colestriler/codex-micro-diy-guide/pcb/led-driver-rev-a/board-top.png

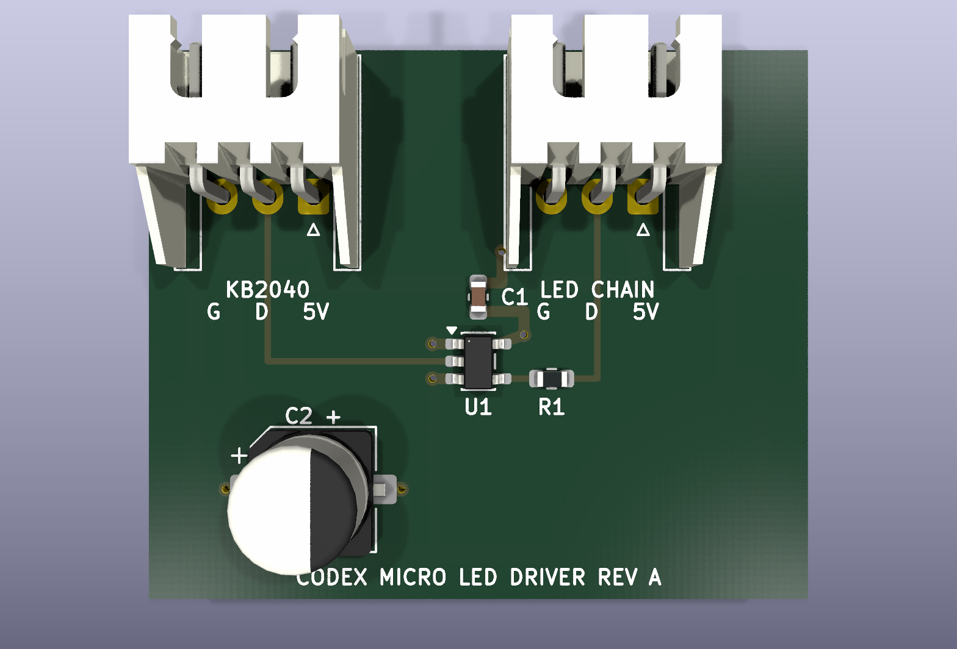
pcb/led-driver-rev-a/board-top.png
