colestriler/codex-micro-diy-guide/public/downloads/joystick-flat-v3/preview.png

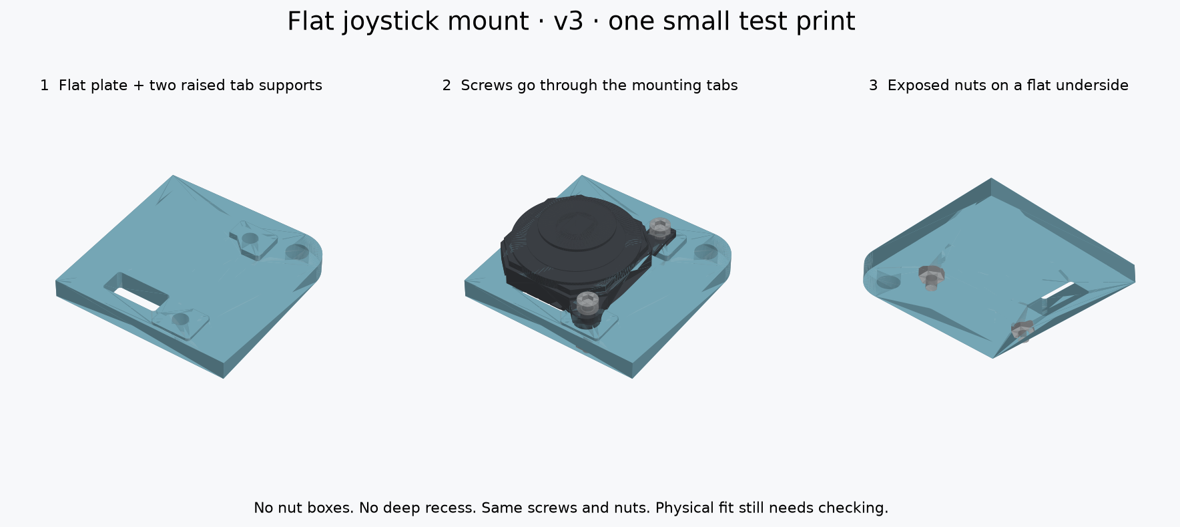
public/downloads/joystick-flat-v3/preview.png
