colestriler/codex-micro-diy-guide/public/downloads/mounting-v5/preview.png

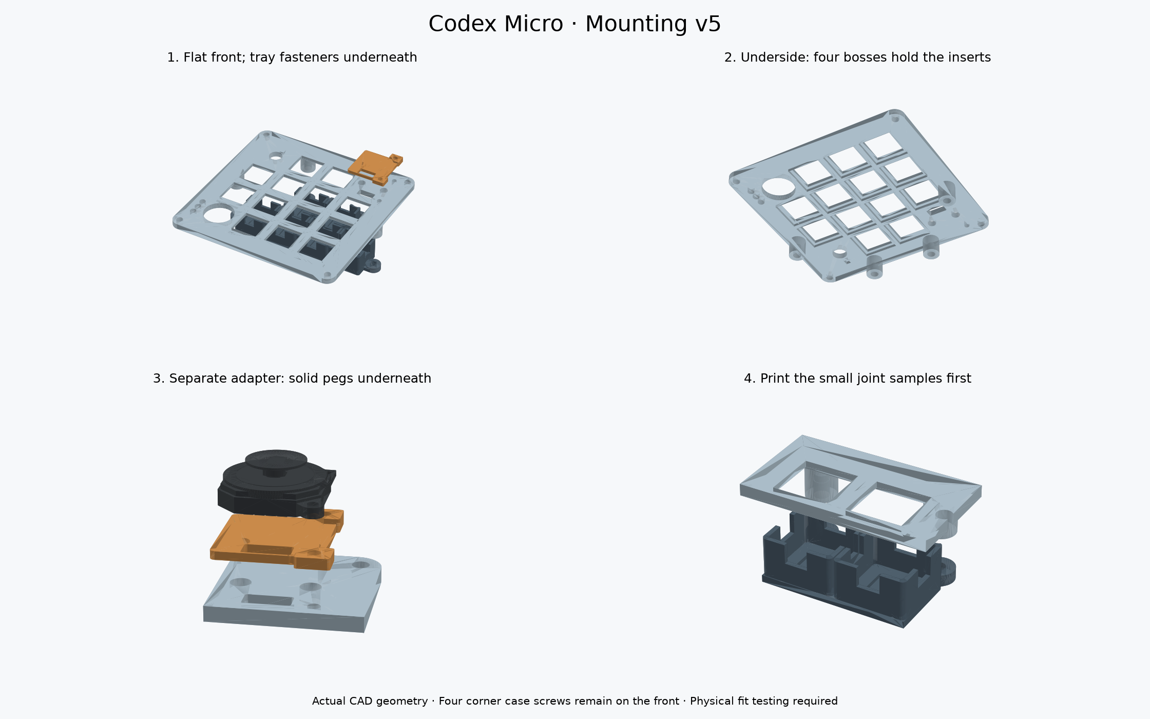
public/downloads/mounting-v5/preview.png
