colestriler/codex-micro-diy-guide/public/downloads/mounting-v5/files/PRINT_FIRST_lower_joint_sample.step

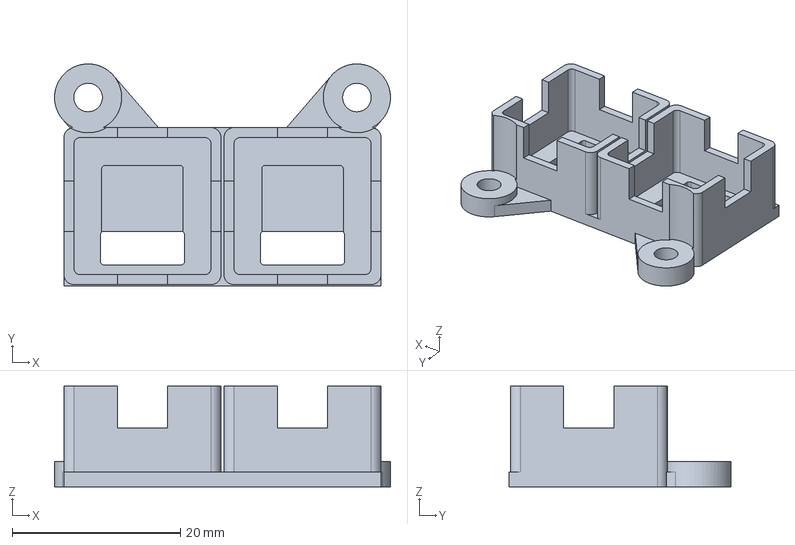
[picture p22: CAD file, 2026-09-16]
public/downloads/mounting-v5/files/PRINT_FIRST_lower_joint_sample.step
40.0 x 26.4 x 12.0 mm
