colestriler/codex-micro-diy-guide/public/downloads/mounting-v5/references/tray-v4.step

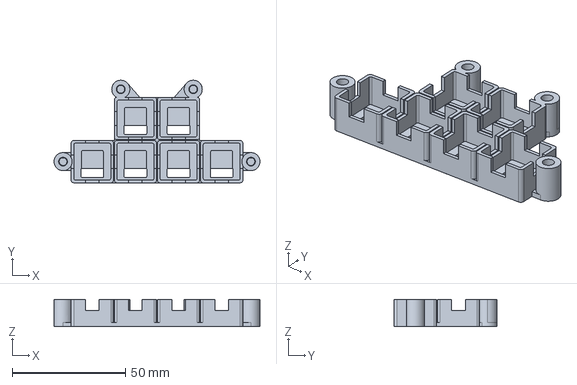
[picture p23: CAD file, 2026-09-15]
public/downloads/mounting-v5/references/tray-v4.step
91.0 x 45.3 x 12.0 mm
