colestriler/codex-micro-diy-guide/public/downloads/baffle-snap-v1/files/PRINT_ONE_test_plate_with_clips.step

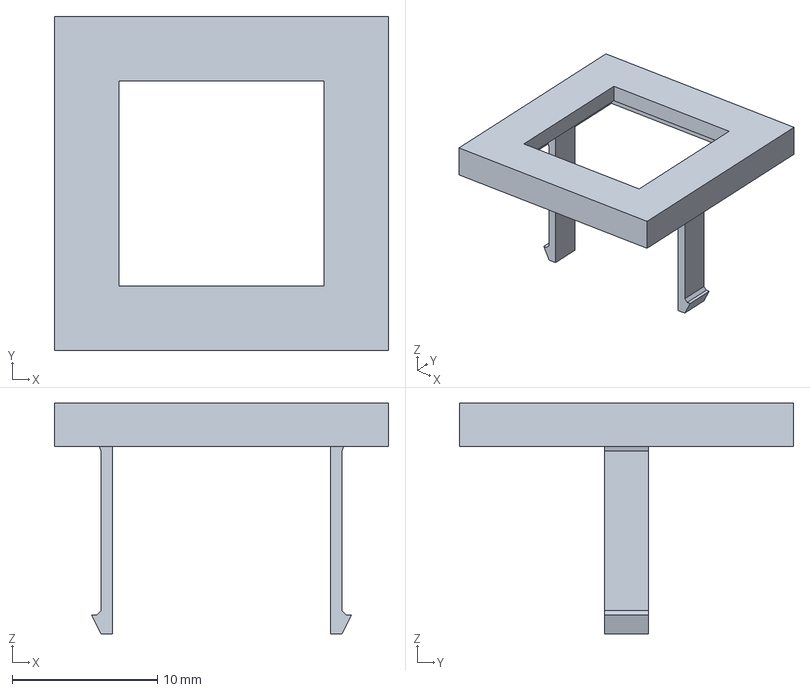
[picture p24: CAD file, 2026-09-15]
public/downloads/baffle-snap-v1/files/PRINT_ONE_test_plate_with_clips.step
23.0 x 23.0 x 15.9 mm
