colestriler/codex-micro-diy-guide/public/downloads/baffle-tray-v4/files/PRINT_FIRST_two_key_top_sample.step

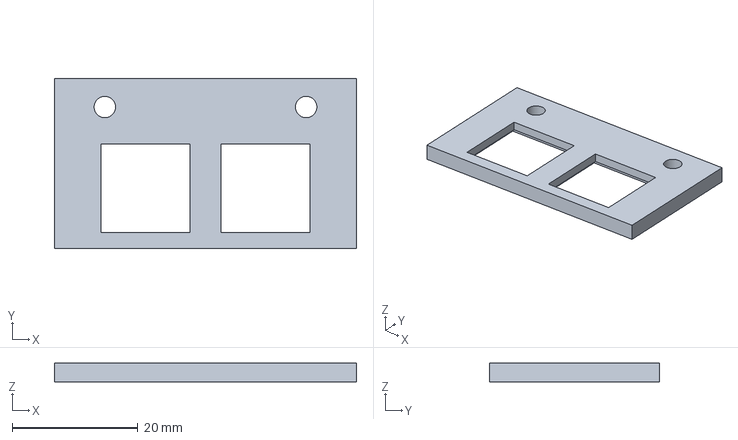
[picture p25: CAD file, 2026-09-15]
public/downloads/baffle-tray-v4/files/PRINT_FIRST_two_key_top_sample.step
48.0 x 26.9 x 3.00 mm
