colestriler/codex-micro-diy-guide/public/downloads/joystick-fit-v1/files/holder.step

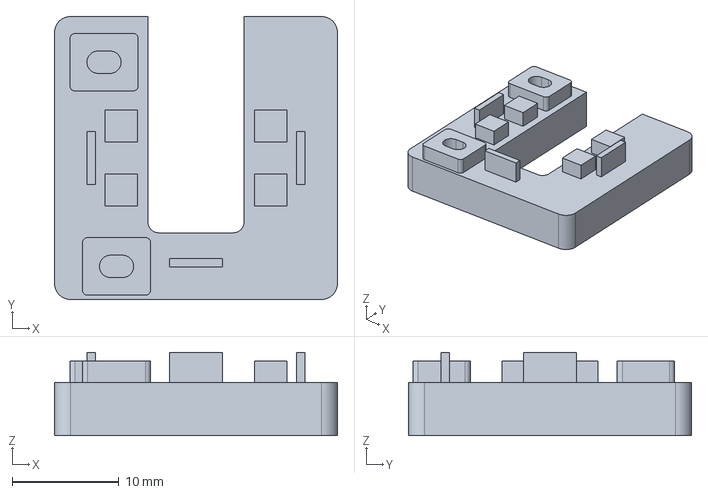
[picture p26: CAD file, 2026-09-14]
public/downloads/joystick-fit-v1/files/holder.step
26.5 x 26.5 x 7.80 mm
