colestriler/codex-micro-diy-guide/public/downloads/mounting-v5/files/PRINT_FIRST_joystick_corner.step

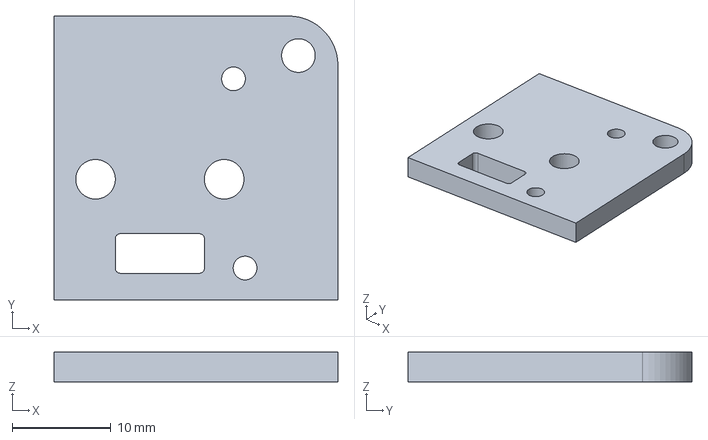
[picture p27: CAD file, 2026-09-16]
public/downloads/mounting-v5/files/PRINT_FIRST_joystick_corner.step
28.7 x 28.7 x 3.00 mm
