colestriler/codex-micro-diy-guide/public/downloads/mounting-v5/references/joystick-reference.step

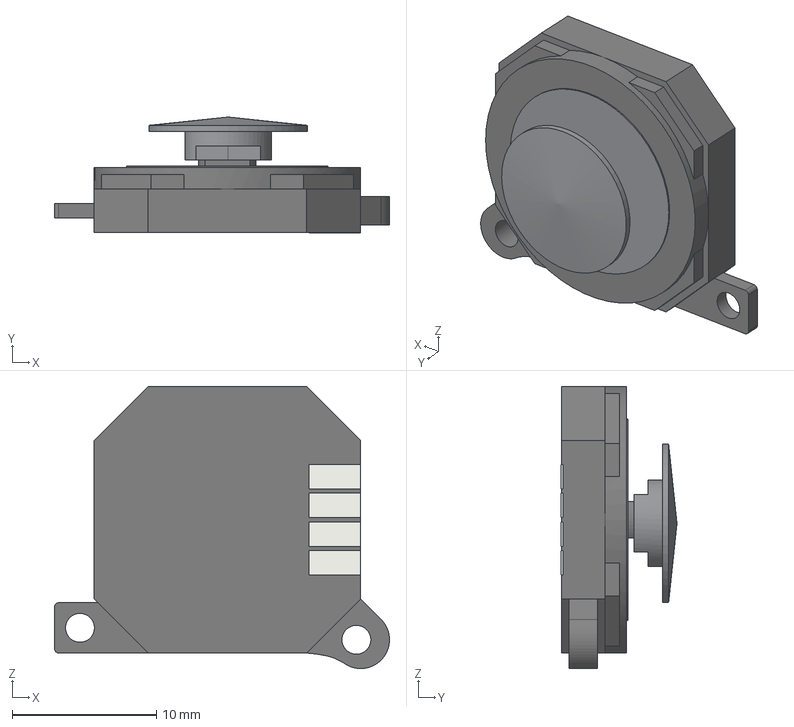
[picture p28: CAD file, 2026-09-14]
public/downloads/mounting-v5/references/joystick-reference.step
23.2 x 8.05 x 19.6 mm
