colestriler/codex-micro-diy-guide/public/downloads/step/07_light_tray_v5_WAIT.step

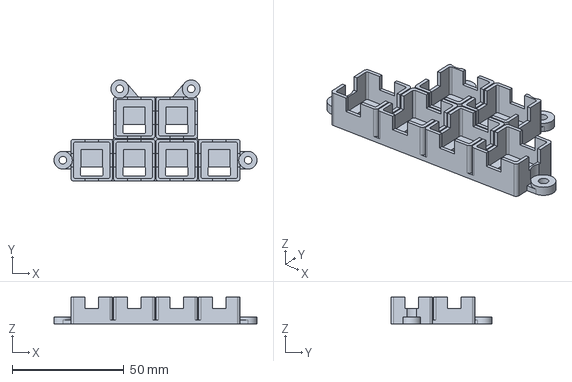
[picture p29: CAD file, 2026-09-16]
public/downloads/step/07_light_tray_v5_WAIT.step
91.0 x 45.3 x 12.0 mm
