colestriler/codex-micro-diy-guide/public/downloads/baffle-tray-v4/files/PRINT_FIRST_two_key_baffle_sample.step

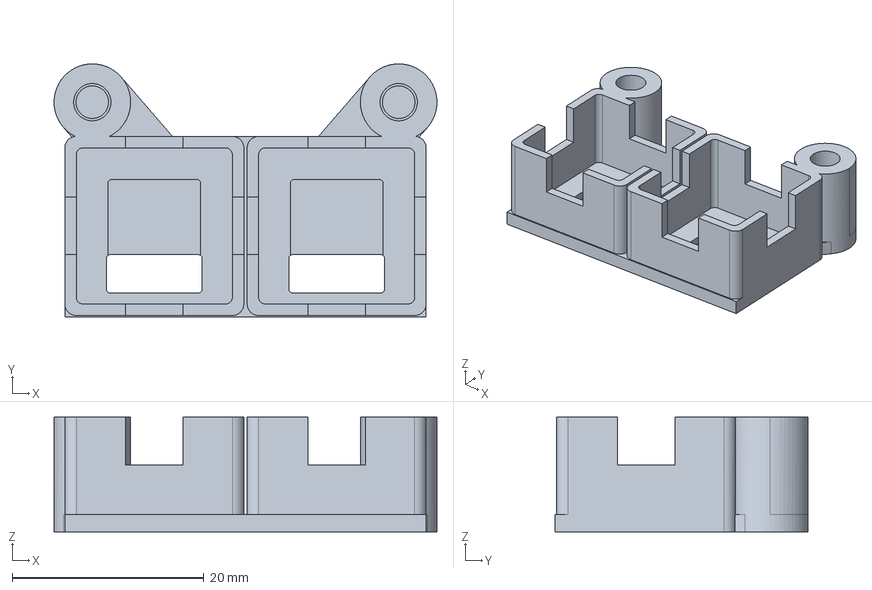
[picture p30: CAD file, 2026-09-15]
public/downloads/baffle-tray-v4/files/PRINT_FIRST_two_key_baffle_sample.step
40.0 x 26.4 x 12.0 mm
