colestriler/codex-micro-diy-guide/public/downloads/joystick-fit-v1/files/shim_B_0.5mm.step

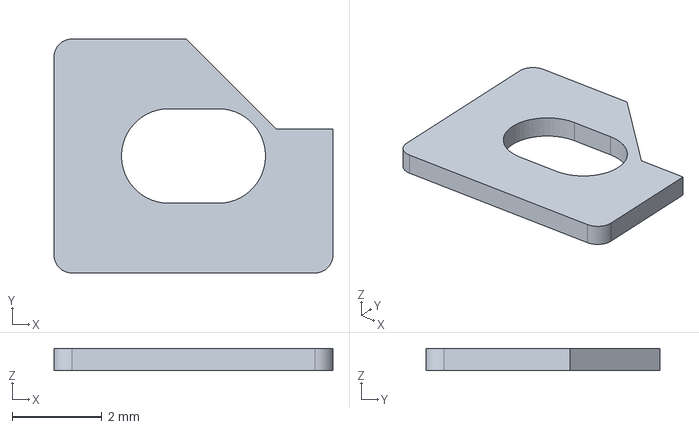
[picture p31: CAD file, 2026-09-14]
public/downloads/joystick-fit-v1/files/shim_B_0.5mm.step
6.20 x 5.20 x 0.5 mm
