colestriler/codex-micro-diy-guide/public/downloads/joystick-integrated-v2/files/PRINT_FIRST_joystick_corner_v2.step

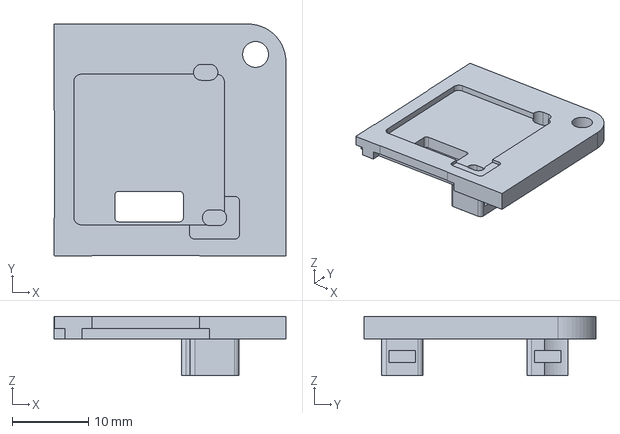
[picture p32: CAD file, 2026-09-14]
public/downloads/joystick-integrated-v2/files/PRINT_FIRST_joystick_corner_v2.step
30.5 x 30.5 x 7.80 mm
