colestriler/codex-micro-diy-guide/public/downloads/mounting-v5/references/case.step

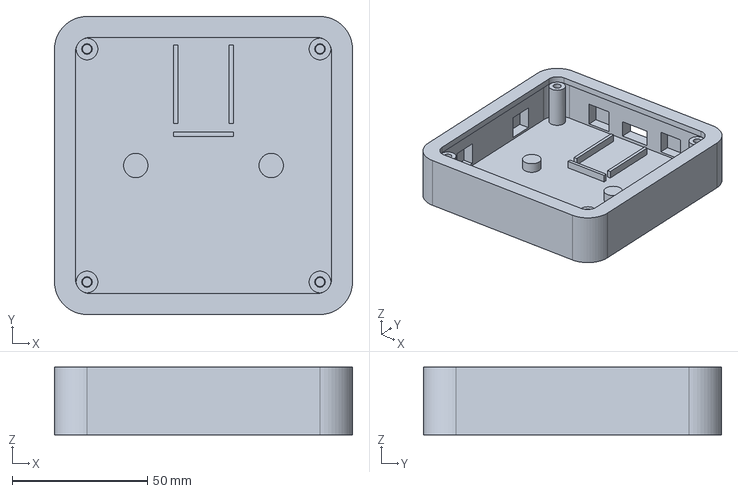
[picture p33: CAD file, 2026-09-06]
public/downloads/mounting-v5/references/case.step
110.0 x 110.0 x 25.0 mm
