colestriler/codex-micro-diy-guide/public/downloads/mounting-v5/references/original-plate.step

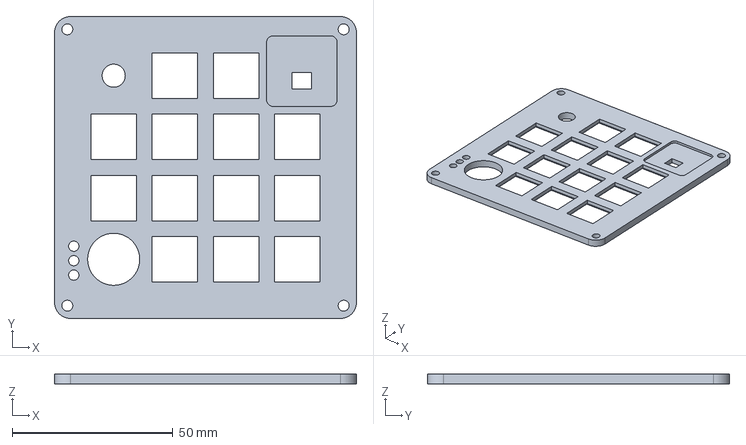
[picture p34: CAD file, 2026-09-06]
public/downloads/mounting-v5/references/original-plate.step
94.0 x 94.0 x 3.00 mm
