colestriler/codex-micro-diy-guide/public/downloads/mounting-v5/files/PRINT_FIRST_upper_joint_sample.step

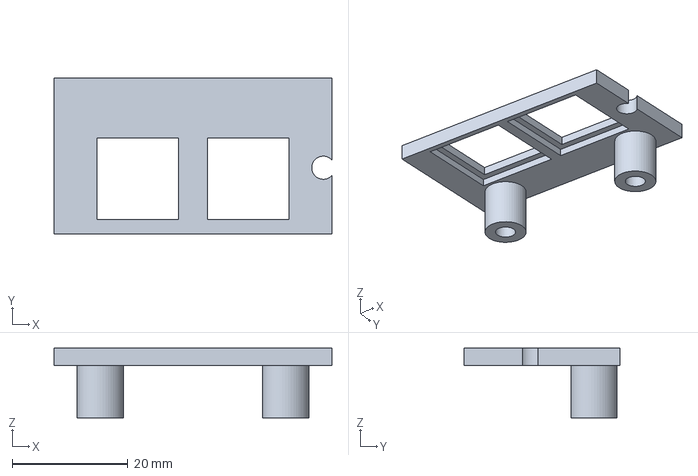
[picture p36: CAD file, 2026-09-16]
public/downloads/mounting-v5/files/PRINT_FIRST_upper_joint_sample.step
48.0 x 26.9 x 12.0 mm
