colestriler/codex-micro-diy-guide/public/downloads/step/04_joystick_adapter_v5.step

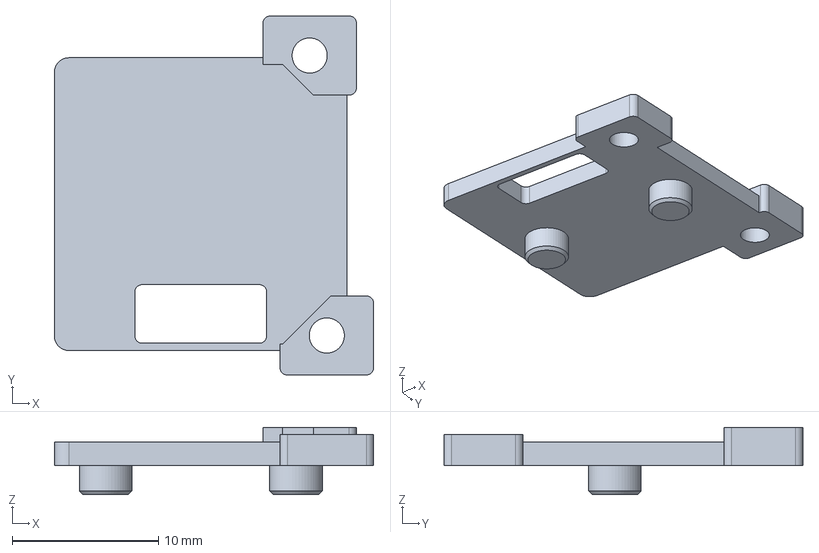
[picture p37: CAD file, 2026-09-16]
public/downloads/step/04_joystick_adapter_v5.step
21.8 x 24.5 x 4.60 mm
