colestriler/codex-micro-diy-guide/public/downloads/joystick-fit-v1/files/shim_B_1.0mm.step

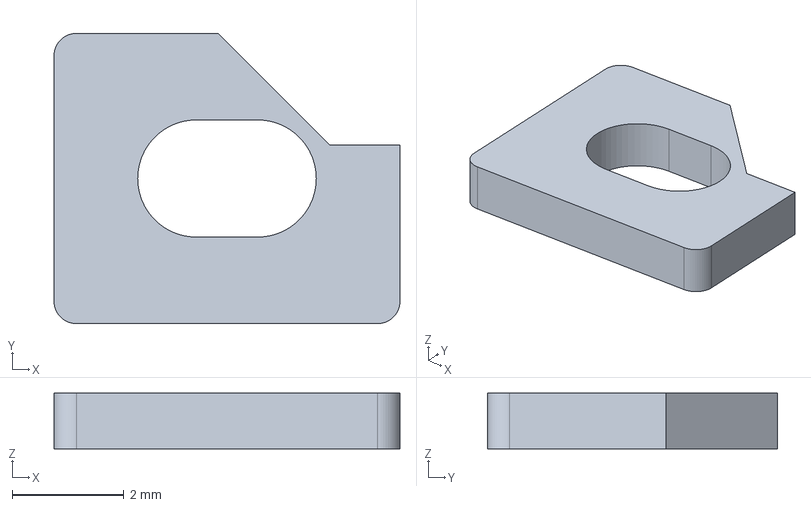
[picture p38: CAD file, 2026-09-14]
public/downloads/joystick-fit-v1/files/shim_B_1.0mm.step
6.20 x 5.20 x 1.00 mm
