colestriler/codex-micro-diy-guide/public/downloads/step/07_heatset_six_light_tray_v3_WAIT.step

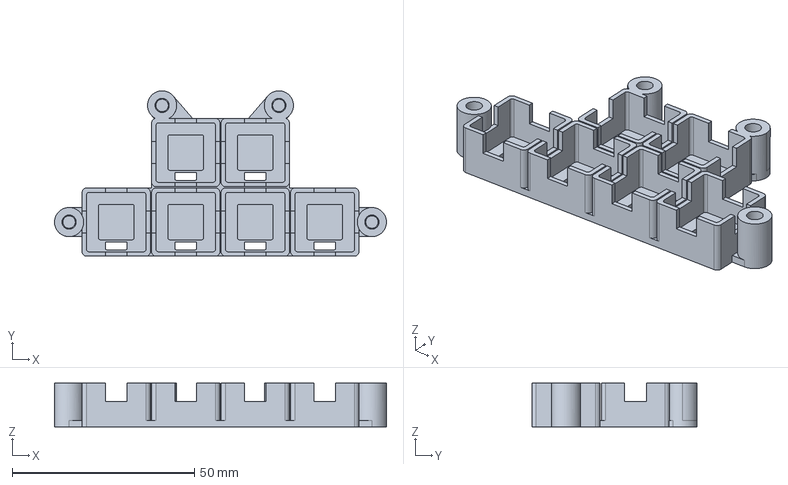
[picture p39: CAD file, 2026-09-15]
public/downloads/step/07_heatset_six_light_tray_v3_WAIT.step
91.0 x 45.3 x 12.0 mm
