colestriler/codex-micro-diy-guide/public/downloads/step/07_two_layer_baffle_sample.step

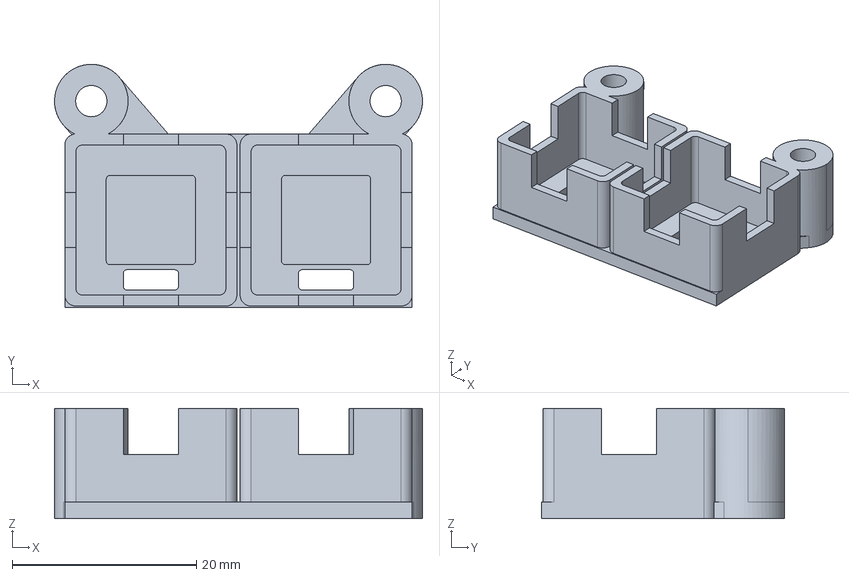
[picture p40: CAD file, 2026-09-15]
public/downloads/step/07_two_layer_baffle_sample.step
40.0 x 26.4 x 12.0 mm
