colestriler/codex-micro-diy-guide/public/downloads/step/09_keycap_2u_dual_stem.step

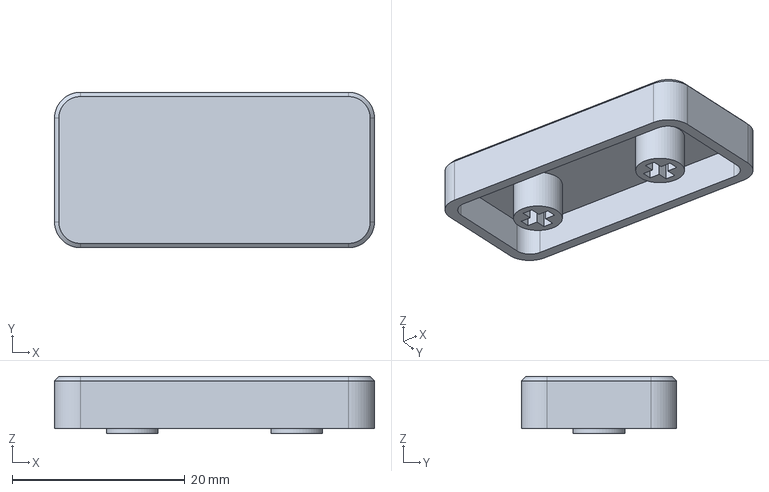
[picture p41: CAD file, 2026-09-13]
public/downloads/step/09_keycap_2u_dual_stem.step
37.0 x 18.0 x 6.60 mm
