colestriler/codex-micro-diy-guide/public/downloads/step/08_keycap_1u.step

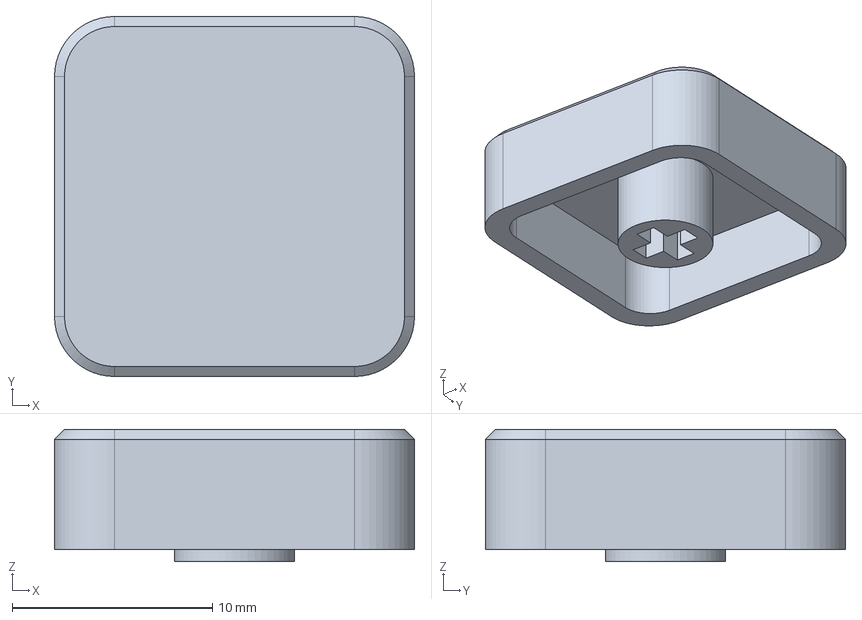
[picture p42: CAD file, 2026-09-13]
public/downloads/step/08_keycap_1u.step
18.0 x 18.0 x 6.60 mm
