colestriler/codex-micro-diy-guide/public/downloads/step/05_touch_cap.step

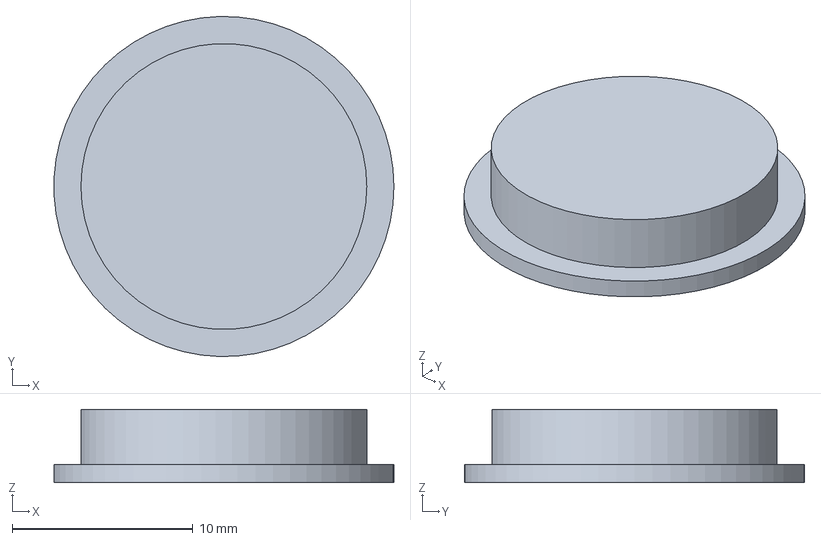
[picture p43: CAD file, 2026-09-06]
public/downloads/step/05_touch_cap.step
18.8 x 18.8 x 4.05 mm
