colestriler/codex-micro-diy-guide/public/downloads/step/04_joystick_cradle.step

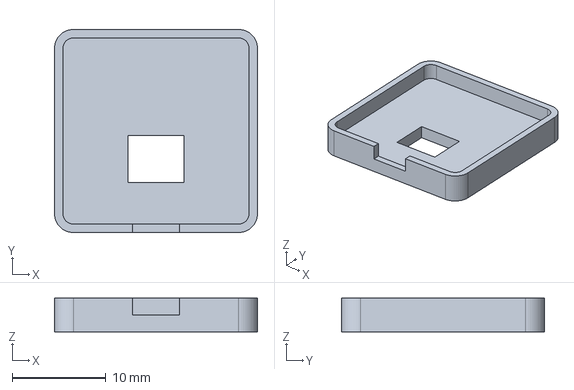
[picture p44: CAD file, 2026-09-06]
public/downloads/step/04_joystick_cradle.step
21.6 x 21.6 x 3.60 mm
