colestriler/codex-micro-diy-guide/public/downloads/step/11_stem_insert_coupon.step

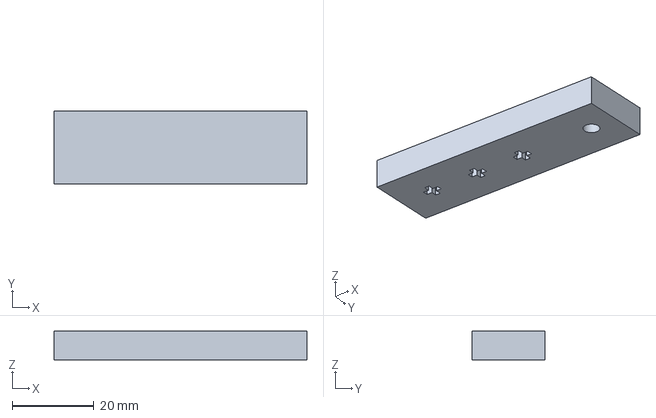
[picture p45: CAD file, 2026-09-06]
public/downloads/step/11_stem_insert_coupon.step
62.0 x 18.0 x 7.00 mm
