colestriler/codex-micro-diy-guide/public/downloads/step/03_round_foot.step

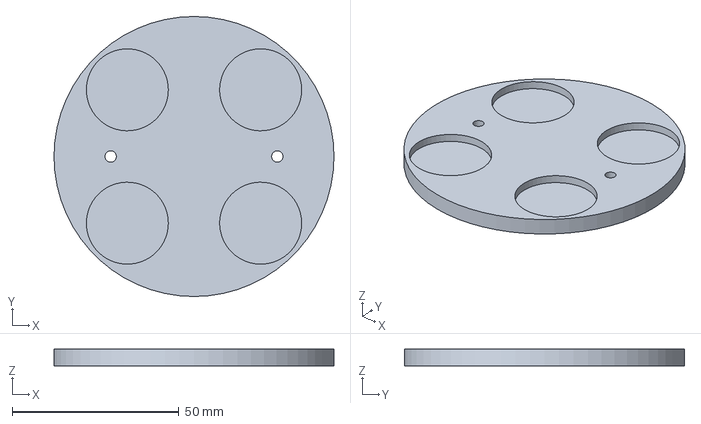
[picture p46: CAD file, 2026-09-06]
public/downloads/step/03_round_foot.step
84.0 x 84.0 x 5.00 mm
