colestriler/codex-micro-diy-guide/public/downloads/step/06_encoder_knob.step

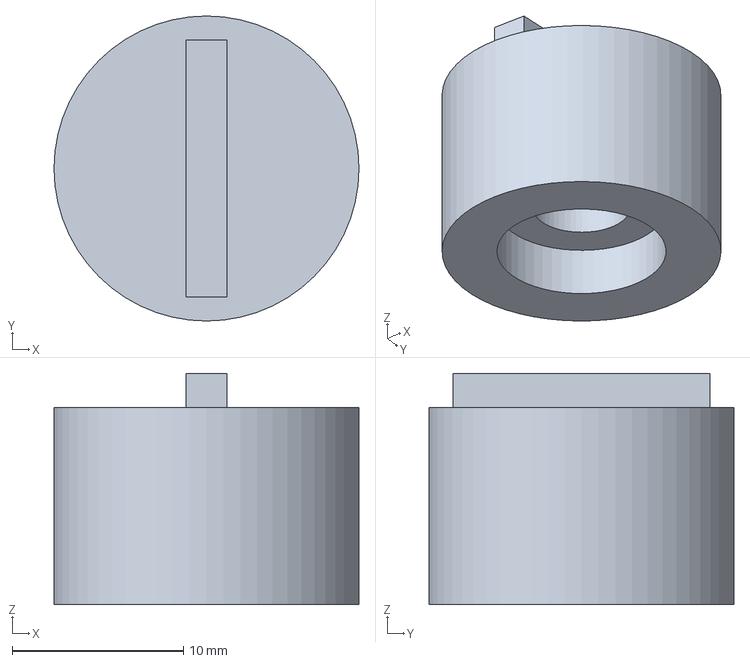
[picture p47: CAD file, 2026-09-06]
public/downloads/step/06_encoder_knob.step
17.8 x 17.8 x 13.5 mm
