colestriler/codex-micro-diy-guide/public/downloads/step/10_switch_fit_coupon.step

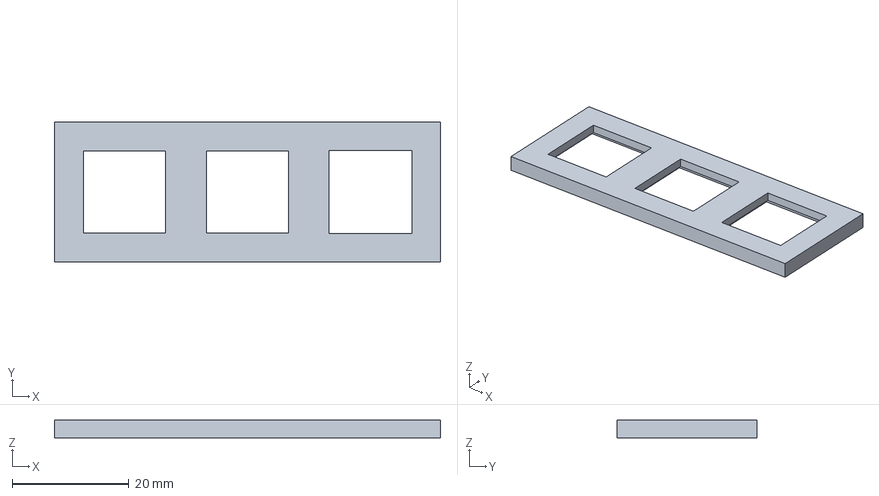
[picture p48: CAD file, 2026-09-06]
public/downloads/step/10_switch_fit_coupon.step
66.0 x 24.0 x 3.00 mm
