colestriler/codex-micro-diy-guide/public/downloads/wiring-guide/board-all.png

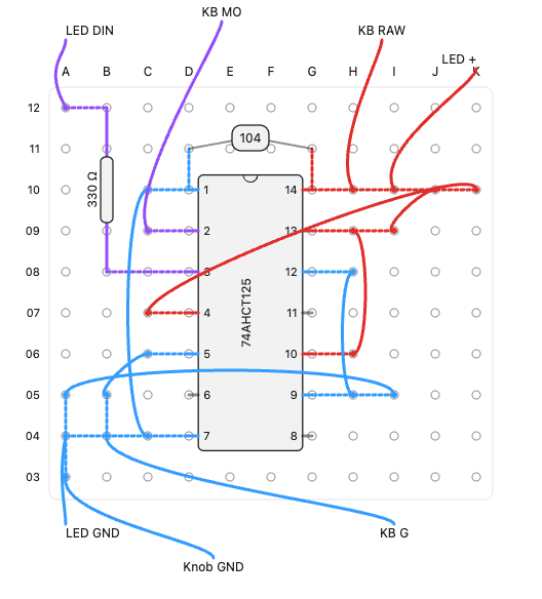
public/downloads/wiring-guide/board-all.png
