colestriler/codex-micro-diy-guide/public/downloads/wiring-guide/board-ground.png

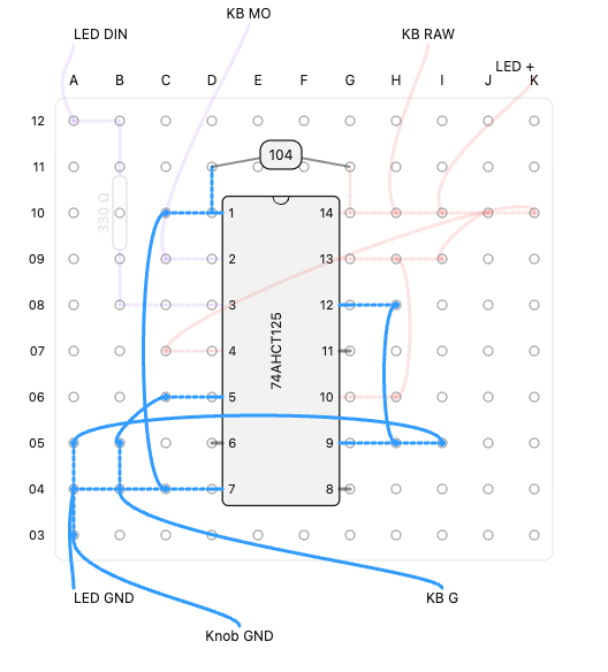
public/downloads/wiring-guide/board-ground.png
