colestriler/codex-micro-diy-guide/public/downloads/wiring-guide/board-power.png

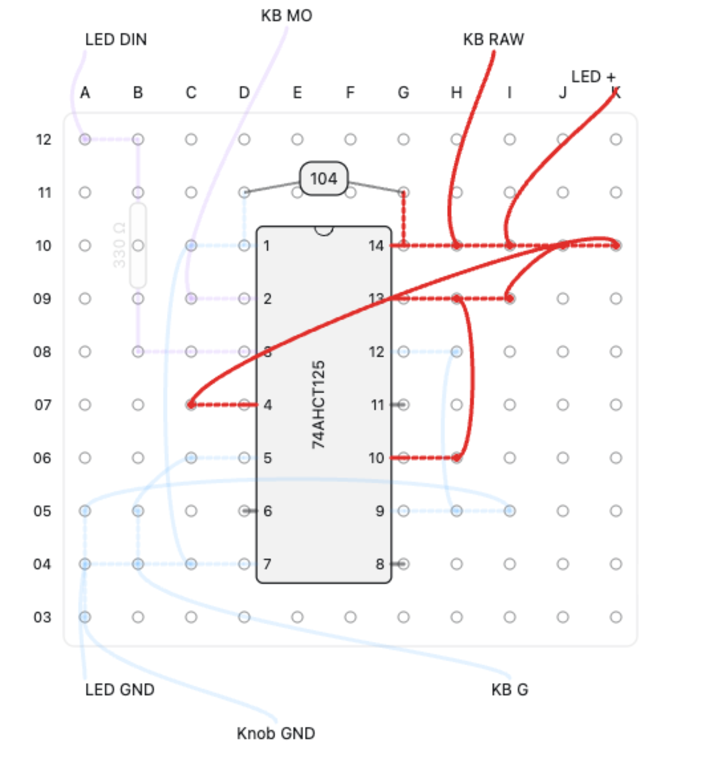
public/downloads/wiring-guide/board-power.png
