colestriler/codex-micro-diy-guide/public/downloads/wiring-guide/board-signal.png

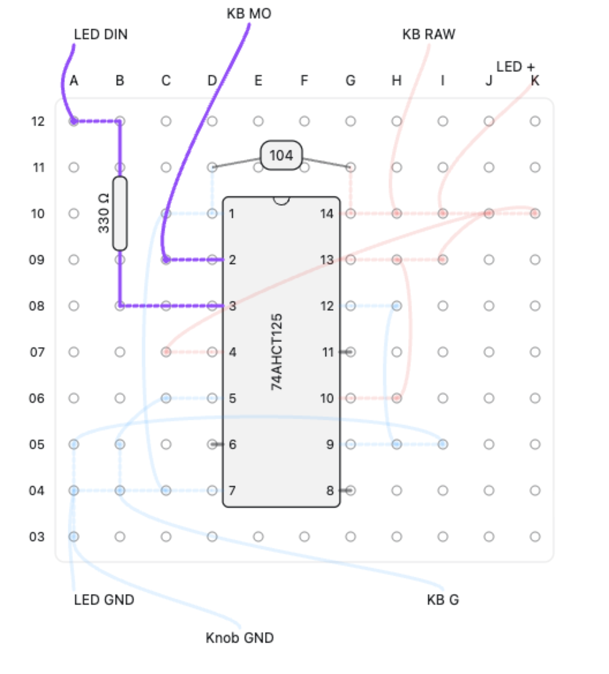
public/downloads/wiring-guide/board-signal.png
