colestriler/codex-micro-diy-guide/public/downloads/wiring-guide/complete-keyboard-preview.png

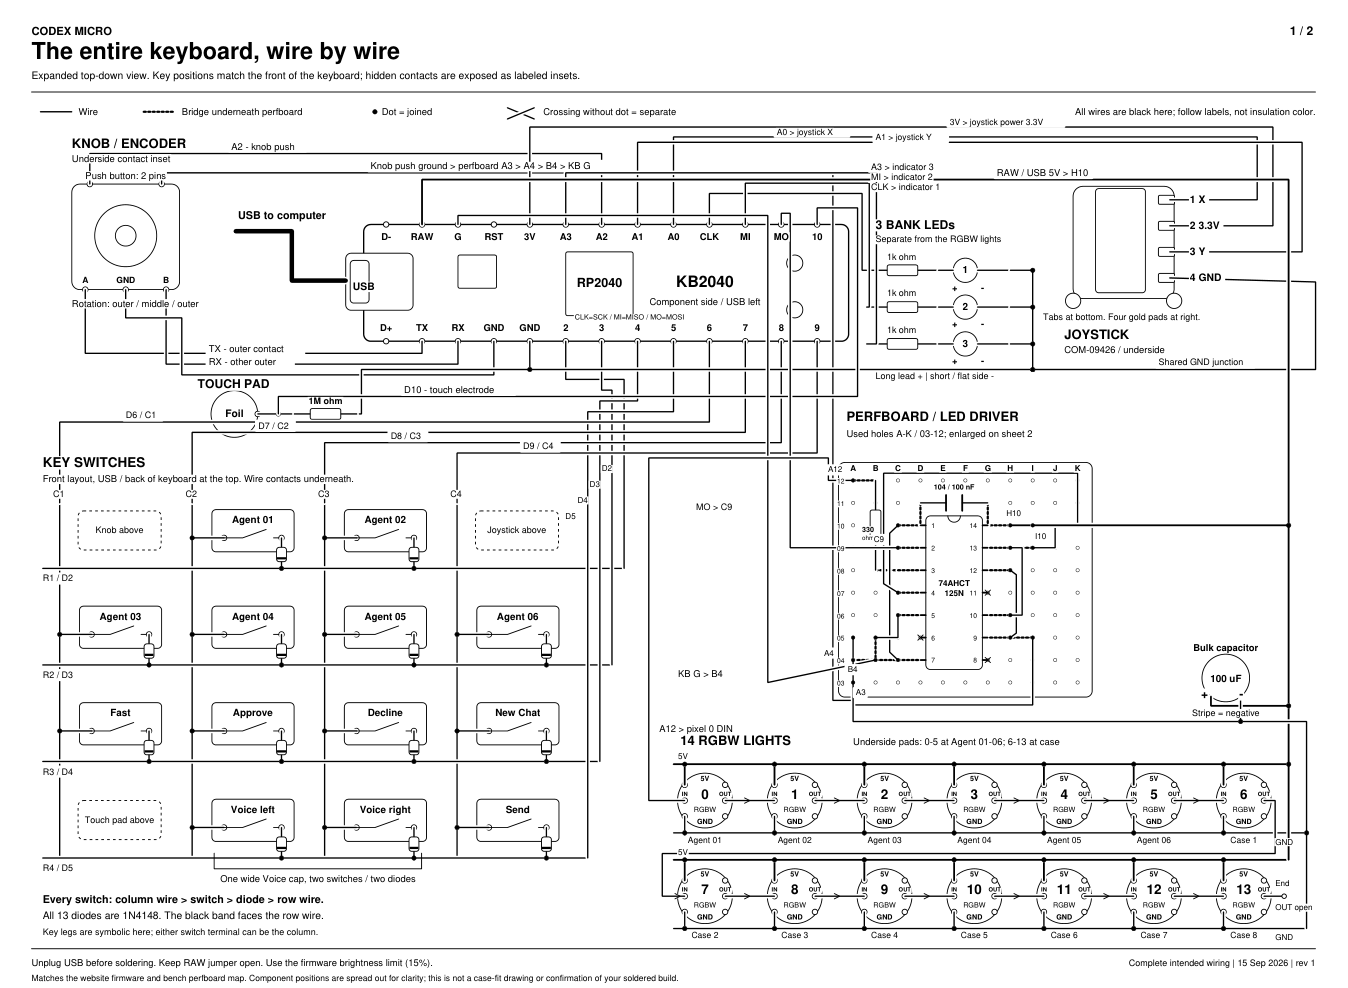
public/downloads/wiring-guide/complete-keyboard-preview.png
