colestriler/codex-micro-diy-guide/public/images/wiring/encoder.jpg

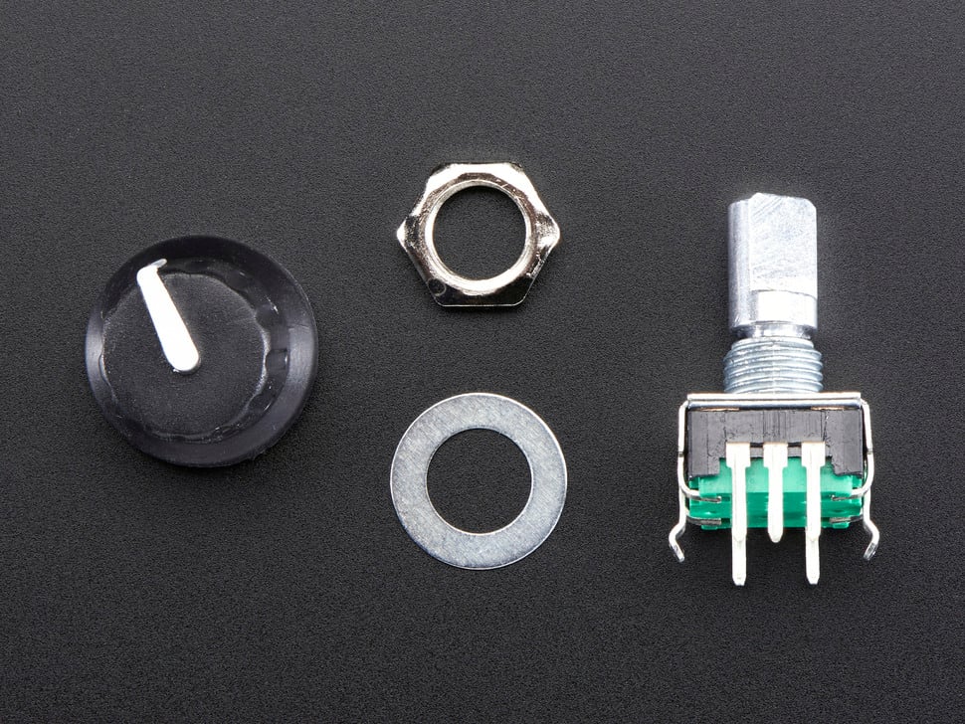
public/images/wiring/encoder.jpg
