colestriler/codex-micro-diy-guide/public/images/wiring/pixels.jpg

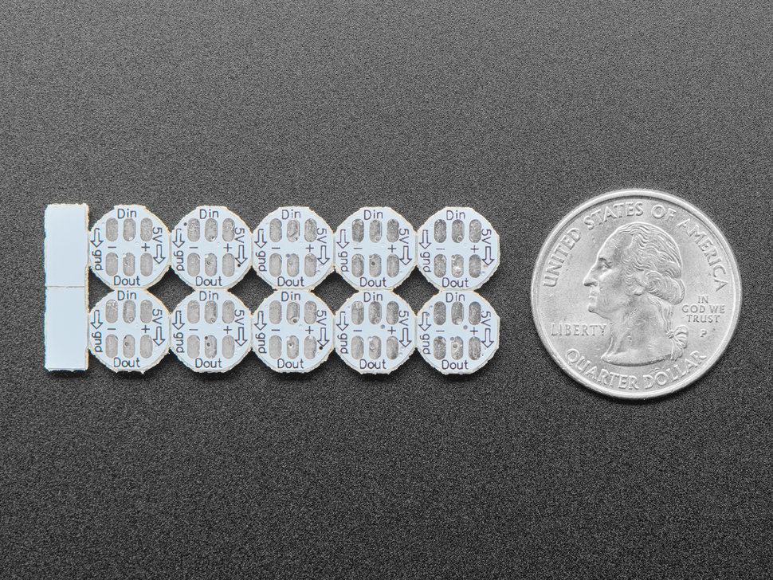
public/images/wiring/pixels.jpg
