colestriler/codex-micro-diy-guide/public/downloads/tools/make_guide.py

from pathlib import Path
import csv,json,base64,html,zipfile,io
ROOT=Path(__file__).resolve().parents[1]
PARTS=json.loads((ROOT/'docs/parts.json').read_text())

def dl(path,label=None):
    p=ROOT/path
    if not p.exists():raise FileNotFoundError(p)
    mime='application/octet-stream'
    return '<a download="'+html.escape(p.name)+'" href="data:'+mime+';base64,'+base64.b64encode(p.read_bytes()).decode()+'">'+html.escape(label or p.name)+'</a>'

def link(url,label):return '<a href="'+html.escape(url)+'" target="_blank" rel="noopener">'+label+' ↗</a>'
rows=''
materials={'01_case':'Clear / natural PETG','02_switch_plate':'White or clear PETG','03_round_foot':'White or gray PETG','04_joystick_cradle':'Black PETG','05_touch_cap':'Black PETG','06_encoder_knob':'White PETG','07_led_baffle':'Black PETG','08_keycap_1u':'6 clear + 5 white PETG','09_keycap_2u_dual_stem':'White PETG','10_switch_fit_coupon':'Same as plate','11_stem_insert_coupon':'Same as cap / case'}
for name,p in PARTS.items():
    rows+=f'<tr><td><strong>{html.escape(name.replace("_"," "))}</strong><small>{html.escape(p["notes"])}</small></td><td>{p["qty"]}</td><td>{materials[name]}</td><td>{dl("stl/"+name+".stl","STL")} · {dl("step/"+name+".step","STEP")}</td></tr>'
bom=''
for r in csv.DictReader((ROOT/'docs/bom.csv').open()):
    bom+=f'<tr data-route="{r["route"]}"><td><input type="checkbox" aria-label="Bought {html.escape(r["item"])}"></td><td><strong>{link(r["url"],html.escape(r["item"]))}</strong><small>{html.escape(r["notes"])}</small></td><td>{r["quantity_to_buy"]}<small>Use: {r["quantity_used"]}</small></td><td>{r["estimated_USD"]}</td><td><span class="tag">{r["route"]}</span></td></tr>'
# Embedded download makes the HTML usable as a single self-contained file.
packed=io.BytesIO()
with zipfile.ZipFile(packed,'w',zipfile.ZIP_DEFLATED) as z:
    for folder in ['cad','stl','step','firmware','tools','docs','animation']:
        for p in sorted((ROOT/folder).rglob('*')):
            if p.is_file() and '__pycache__' not in p.parts and p.name!='make_guide.py':z.write(p,p.relative_to(ROOT))
    for n in ['README.md','requirements.txt','assembly-animation.html']:z.write(ROOT/n,n)
zip_data=base64.b64encode(packed.getvalue()).decode()
preview=base64.b64encode((ROOT/'docs/cad-preview.png').read_bytes()).decode()
wiring=(ROOT/'docs/wiring.svg').read_text()
page='''<!doctype html>
<html lang="en"><head><meta charset="utf-8"><meta name="viewport" content="width=device-width, initial-scale=1"><title>DIY Micro — Full Build Specification</title>
<style>
:root{--ink:#152e2b;--muted:#5c7069;--paper:#f4f4ee;--line:#d6dfd7;--green:#b9d7ac;--dark:#163c33;--amber:#f4d496}*{box-sizing:border-box}html{scroll-behavior:smooth;scroll-padding-top:86px}body{margin:0;background:var(--paper);color:var(--ink);font:16px/1.65 -apple-system,BlinkMacSystemFont,"Segoe UI",sans-serif}a{color:#25614d;text-underline-offset:4px}a:hover{color:#102f23}button,input{font:inherit}button{cursor:pointer}header{position:sticky;top:0;background:rgba(244,244,238,.97);z-index:5;border-bottom:1px solid var(--line);padding:16px 4vw;display:flex;align-items:center;gap:26px}header .brand{font-weight:800;letter-spacing:-.6px;white-space:nowrap}nav{display:flex;gap:22px;overflow:auto;white-space:nowrap;font-size:13px;flex:1}nav a{text-decoration:none;color:var(--muted)}.print{border:1px solid var(--line);background:transparent;border-radius:6px;padding:6px 12px;font-size:12px}.wrap{max-width:1240px;margin:auto;padding:0 40px}section{padding:65px 0;border-bottom:1px solid var(--line)}.eyebrow{font:12px/1.4 ui-monospace,monospace;letter-spacing:1.6px;text-transform:uppercase;color:var(--muted)}h1{font-size:clamp(45px,6.2vw,86px);line-height:1.03;letter-spacing:-4.5px;font-weight:600;margin:23px 0}h2{font-size:36px;line-height:1.16;letter-spacing:-1.3px;font-weight:600;margin:14px 0 22px}h3{font-size:20px;letter-spacing:-.4px;margin:8px 0 12px}p{margin:12px 0}.lead{font-size:19px;line-height:1.6;color:var(--muted);max-width:620px}.hero{display:grid;grid-template-columns:1fr 1fr;gap:45px;align-items:center;padding:70px 0 42px}.hero-copy p{max-width:540px}.actions{display:flex;gap:12px;flex-wrap:wrap;margin:26px 0}.actions a,.primary{padding:11px 18px;border:1px solid var(--ink);border-radius:6px;text-decoration:none;font-size:14px;font-weight:600}.actions a:first-child,.primary{background:var(--dark);color:#fff}.meta{display:flex;gap:23px;font:12px ui-monospace,monospace;flex-wrap:wrap;color:var(--muted)}.notice{border-left:4px solid #b68a37;background:#ede7d6;padding:18px 22px;margin:24px 0}.notice strong{display:block;margin-bottom:4px}.note{background:#e6ece2;border:1px solid #cbd8c5;border-radius:8px;padding:20px 24px}.grid2{display:grid;grid-template-columns:1fr 1fr;gap:24px}.grid3{display:grid;grid-template-columns:repeat(3,1fr);gap:20px}.card{padding:25px;border:1px solid var(--line);border-radius:10px;background:#fafbf6}.tag{display:inline-block;font:11px ui-monospace,monospace;text-transform:uppercase;letter-spacing:.7px;background:#e5eade;color:#385245;padding:4px 7px;border-radius:4px}.tag.gold{background:#f2dfb8;color:#65511a}.card p{color:var(--muted)}.table-wrap{overflow:auto}table{border-collapse:collapse;width:100%;font-size:14px;text-align:left}th{font-size:11px;text-transform:uppercase;letter-spacing:1px;color:var(--muted);padding:12px 14px;background:#e6ece2}td{padding:16px 14px;border-bottom:1px solid var(--line);vertical-align:top}td small{display:block;font-size:12px;color:var(--muted);line-height:1.5;margin-top:5px}td:last-child{white-space:nowrap}small,.caption{font-size:12px;color:var(--muted)}code{background:#e5eae0;padding:2px 5px;border-radius:3px;font-size:13px}pre{background:#203b33;color:#ecf3e6;border-radius:8px;padding:22px;overflow:auto;font:13px/1.7 ui-monospace,monospace}pre code{background:none;padding:0;color:inherit}ul,ol{padding-left:22px}li{margin:9px 0}.steps{counter-reset:step;display:grid;grid-template-columns:1fr 1fr;gap:18px}.step{border:1px solid var(--line);background:#fafbf6;padding:24px;border-radius:8px}.step:before{counter-increment:step;content:counter(step,decimal-leading-zero);font:12px ui-monospace,monospace;color:#7c8f77;display:block;margin-bottom:10px}.step p{color:var(--muted);font-size:14px}.wide{grid-column:1/-1}.preview{display:block;width:100%;border-radius:9px}.downloads{display:flex;gap:18px;flex-wrap:wrap;margin:15px 0;font-size:14px}.swatch{height:85px;border-radius:6px;margin:16px 0;border:1px solid #d5dbd1}.clear{background:repeating-linear-gradient(115deg,#dce4da70 0 1px,#f9fcf870 1px 5px),linear-gradient(130deg,#d0e3da,#f5f7f2)}.white{background:#f9faf5}.black{background:#262f2a}.filters{display:flex;gap:8px;margin:20px 0;flex-wrap:wrap}.filters button,.status-btn{border:1px solid var(--line);border-radius:30px;padding:7px 15px;background:transparent;font-size:12px}.filters button.active{background:var(--dark);color:white}.sim{background:#dbe5d7;border-radius:16px;padding:30px;position:relative}.device{width:min(100%,380px);margin:10px auto 25px;padding:32px;background:linear-gradient(135deg,#f9faf5,#bec9c1);border:2px solid #eaf1e8;box-shadow:8px 20px 32px #52665529,0 8px 0 #9daea1;border-radius:36px;position:relative}.device-grid{display:grid;grid-template-columns:repeat(4,1fr);gap:7px;padding:8px;background:#e4e9e2;border-radius:13px}.key{aspect-ratio:1;border:1px solid #f7faf3;border-radius:12px;background:linear-gradient(135deg,#f9fbf4,#e1e7dc);color:#18392d;box-shadow:0 4px 0 #b4c0b1;display:flex;align-items:center;justify-content:center;font-size:22px;padding:0}.key svg{width:24px;height:24px;fill:none;stroke:currentColor;stroke-width:1.7;stroke-linecap:round;stroke-linejoin:round}.key.agent{background:radial-gradient(circle,var(--glow,#398cf0) 0,#ffffff36 72%),#c0d0ca;box-shadow:0 4px 0 #9dafaa,inset 0 0 20px var(--glow,#398cf0);font:11px ui-monospace,monospace;color:#19392e}.key.agent.selected{outline:2px solid #214d3c;outline-offset:2px}.key.knob{border-radius:50%;transform:rotate(35deg);font-size:36px}.key.joy{border-radius:50%;background:#26342c;border:5px solid #4e5f52;color:#a3b8a8;box-shadow:0 3px 0 #16291d;font-size:15px}.key.touch{border:none;background:radial-gradient(circle,#173328 0 30%,#a2b49f 33% 39%,transparent 41%);box-shadow:none}.key.wide-key{grid-column:span 2;aspect-ratio:auto}.sim .caption{text-align:center;margin-top:15px}.status-buttons{display:flex;gap:7px;flex-wrap:wrap;justify-content:center}.status-btn{background:#f4f7ef;display:flex;align-items:center;gap:6px}.dot{display:inline-block;width:8px;height:8px;border-radius:50%;background:var(--c);box-shadow:0 0 0 1px #172c2120}.sim-status{text-align:center;font-size:13px;margin:14px 0 0}.status-line{display:flex;gap:10px;align-items:center;margin:8px 0}.status-line .dot{width:13px;height:13px}.progress{font:12px ui-monospace,monospace;color:var(--muted);margin:15px 0}input[type=checkbox]{accent-color:#39795b;width:16px;height:16px}.checklist label{display:block;padding:9px 0;font-size:14px}.checklist input{vertical-align:middle;margin-right:9px}.diagram svg{width:100%;height:auto}.footer{padding:35px 0 60px;font-size:12px;color:var(--muted)}.assembly-frame{width:100%;height:950px;border:1px solid var(--line);border-radius:10px;background:var(--paper)}@media(max-width:1050px){.assembly-frame{height:1150px}}@media(max-width:600px){.assembly-frame{height:1250px}}@media print{.assembly-frame{display:none}}.callout-number{font-size:35px;letter-spacing:-1px}.muted{color:var(--muted)}.hidden{display:none}@media(max-width:850px){.wrap{padding:0 22px}.hero,.grid2,.grid3,.steps{grid-template-columns:1fr}.hero{padding-top:35px}h1{letter-spacing:-2.5px}header{padding:14px 20px;gap:18px}header .print{display:none}section{padding:45px 0}.sim{max-width:500px;width:100%;margin:auto}td{min-width:100px}td:first-child{min-width:35px}.wide{grid-column:auto}}@media print{header,.actions,.filters,.status-buttons,.downloads,.print{display:none}body{font-size:11px;background:white}.wrap{padding:0}.hero{padding:0;gap:20px}h1{font-size:40px}h2{font-size:25px}section{padding:20px 0}a{color:inherit}td{padding:8px}.card,.step{break-inside:avoid}.sim{padding:15px}.device{max-width:250px;padding:20px}.key{font-size:15px}.notice{background:#eee}.hidden{display:table-row}}
</style></head><body>
<header><div class="brand">DIY / MICRO</div><nav aria-label="Build guide"><a href="#route">Build route</a><a href="#plastic">Plastic</a><a href="#cad">CAD files</a><a href="#parts">Shopping list</a><a href="#animation">Animation</a><a href="#assembly">Assembly</a><a href="#software">Software</a><a href="#checks">Validation</a></nav><button class="print" onclick="window.print()">Print guide</button></header>
<main class="wrap">
<div class="hero"><div class="hero-copy"><div class="eyebrow">Build specification · revision A · 06 Sep 2026</div><h1>Codex Micro.<br>A DIY build.</h1><p class="lead">Recreate the Codex Micro’s layout, tactile controls, and illuminated keys—with editable CAD and a complete parts plan.</p><div class="actions"><a download="DIY-Micro-CAD-and-build-files.zip" href="data:application/zip;base64,__ZIP__">Download all build files ↓</a><a href="#animation">Watch assembly →</a><a href="#route">Read the full-function route</a></div><div class="meta"><span>110 × 110 mm prototype</span><span>13 switches</span><span>6 agent keys</span></div></div>
<div class="sim"><div class="eyebrow">Color behavior / interactive illustration</div><div class="device"><div class="device-grid">
<div class="key knob" title="Reasoning / navigation dial">┃</div><button class="key agent selected" data-agent="0" aria-label="Select agent key 1">01</button><button class="key agent" data-agent="1" aria-label="Select agent key 2">02</button><div class="key joy" title="Planar joystick">✣</div>
<button class="key agent" data-agent="2" aria-label="Select agent key 3">03</button><button class="key agent" data-agent="3" aria-label="Select agent key 4">04</button><button class="key agent" data-agent="4" aria-label="Select agent key 5">05</button><button class="key agent" data-agent="5" aria-label="Select agent key 6">06</button>
<div class="key" title="Fast mode">ϟ</div><div class="key" title="Approve">✓</div><div class="key" title="Decline">×</div><div class="key" title="Continue in new chat">↗</div>
<div class="key touch" title="Touch input"></div><div class="key wide-key" title="Push to talk"><svg viewBox="0 0 24 24"><rect x="9" y="3" width="6" height="12" rx="3"/><path d="M6 11v1a6 6 0 0 0 12 0v-1M12 18v3M9 21h6"/></svg></div><div class="key" title="Send message">↵</div></div></div>
<div class="status-buttons"><button class="status-btn" data-state="idle"><i class="dot" style="--c:#f9faf5"></i>Idle</button><button class="status-btn" data-state="thinking"><i class="dot" style="--c:#4a92ff"></i>Thinking</button><button class="status-btn" data-state="complete"><i class="dot" style="--c:#63ce82"></i>Complete</button><button class="status-btn" data-state="input"><i class="dot" style="--c:#ffbd58"></i>Needs input</button><button class="status-btn" data-state="error"><i class="dot" style="--c:#f3656a"></i>Error</button><button class="status-btn" data-state="off"><i class="dot" style="--c:#8c9b90"></i>Off</button></div><div class="sim-status" aria-live="polite">Agent 01 · Thinking</div><p class="caption">Select a key, then a state. This illustrates color meaning;<br>it is not connected to Codex and is not a color calibration.</p></div></div>
<div class="notice"><strong>Exact functionality is an electronics + software requirement.</strong>The included CAD and KB2040 firmware are a custom prototype. They do <b>not</b> currently deliver native Codex integration. For documented native behavior, use a genuine <b>Creator Micro 2</b> or <b>Codex Micro</b> with its original firmware. Re-housing that board requires measured donor geometry; the current printable case is <b>not a verified donor fit</b>.</div>
<section id="route"><div class="eyebrow">01 / choose the build that meets your requirement</div><h2>Keep the native electronics<br>for native Codex behavior.</h2><p>OpenAI explicitly lists Creator Micro 2 as compatible. The model with Bluetooth is the <b>Pro</b>; the Base is wired. A verified OEM PCB-only kit was not found. If matching the original is the priority, start with a complete genuine unit, verify it works, and customize its enclosure only after measuring it. <a href="https://learn.chatgpt.com/docs/features/codex-micro" target="_blank" rel="noopener">OpenAI compatibility guide ↗</a> · <a href="https://worklouder.cc/creator-micro-2" target="_blank" rel="noopener">Manufacturer specifications ↗</a></p>
<div class="grid2"><article class="card"><span class="tag">Recommended for your requirement</span><h3>Native electronics + printed exterior</h3><p>Retain the factory controller, LEDs, touch electrode, switch assembly, firmware, diffuser, and—on Pro—the original battery and charging circuit. That preserves the supported connection to Codex.</p><p><b>What still needs work:</b> measure the donor PCB, mounting holes, connectors, antenna and diffuser; then revise the case. No donor-compatible enclosure is claimed in this package.</p><p><a href="https://worklouder.cc/creator-micro-2" target="_blank" rel="noopener">Creator Micro 2 Pro ↗</a> · <a href="https://openai.com/supply/co-lab/work-louder/" target="_blank" rel="noopener">Codex Micro ↗</a></p><small>Availability: Codex Micro page showed out of stock ($230). Creator Micro 2 page showed “Not available” without a price. Confirm the selected variant at purchase; no order was placed.</small></article>
<article class="card"><span class="tag gold">Prototype / additional development</span><h3>Custom electronics + supplied CAD</h3><p>USB-C KB2040, hand-wired switches, planar joystick, rotary encoder, capacitive touch, six key LEDs and eight perimeter LEDs. The files below form a buildable prototype design, subject to physical fit and electrical testing.</p><p><b>Included software:</b> USB function keys, dial scroll, joystick arrows, three touch-selected banks, and individually addressable RGBW lights.</p><p><b>Missing for parity:</b> native detection, automatic task status, task switching, voice behavior, reasoning control, app settings, and Bluetooth.</p><small>Custom electronics are not a substitute purchase for the full-function donor route.</small></article></div>
<h3 style="margin-top:32px">Feature acceptance matrix</h3><div class="table-wrap"><table><thead><tr><th>Requirement</th><th>Genuine supported unit</th><th>Included custom prototype</th></tr></thead><tbody>
<tr><td>Native device setup and remapping</td><td>Documented</td><td>Not implemented</td></tr><tr><td>Six task-linked colors and selected-key pulse</td><td>Documented</td><td>LED hardware; manual color commands only</td></tr><tr><td>Task switching, approve / decline / send</td><td>Documented</td><td>Generic F13–F24 keys; app bindings still needed</td></tr><tr><td>Push-to-talk and recording / processing lights</td><td>Documented</td><td>Not implemented; no microphone in the keypad</td></tr><tr><td>Reasoning and composer dial modes</td><td>Documented</td><td>Scroll + Enter only</td></tr><tr><td>Joystick actions and touch input</td><td>Documented</td><td>Arrows + three banks</td></tr><tr><td>Bluetooth and rechargeable battery</td><td>Codex Micro / Creator Micro 2 Pro</td><td>Not included in USB design</td></tr><tr><td>OEM case proportions, finish and feel</td><td>Factory product</td><td>Photo reconstruction; deeper hand-wired body</td></tr></tbody></table></div>
<p class="caption">Native behavior source: <a href="https://learn.chatgpt.com/docs/features/codex-micro">OpenAI’s current setup documentation</a>. Color and behavior changes in future app releases must be tested on the running app. These are separate from the geometry checks performed here.</p></section>
<section id="plastic"><div class="note"><b>Flat keycaps · updated 13 September 2026:</b> Both cap files now have flat finger surfaces, rounded corners and a 0.5 mm beveled rim. File 08 serves the white command caps and clear agent caps; file 09 is the white wide cap. Print the top facing up at 100% scale. Start with 0.10–0.12 mm layers on a 0.4 mm nozzle; support the underside as needed and keep the cross sockets clear. Print a stem-fit coupon and one cap before the full set. Physical fit and finish still need a test print.</div>
<div class="eyebrow">02 / materials</div><h2>Yes—some parts should transmit light.</h2><p class="lead">Buy <b>colorless clear / natural PETG</b> for light transmission. Use opaque white and black where light should be reflected or blocked.</p><div class="grid3"><article class="card"><span class="tag">Light transmission</span><div class="swatch clear"></div><h3>Clear / natural PETG</h3><p>Print the case and six agent keycaps. Its 0.8 mm perimeter windows let the LED colors escape. Clear plate printing is optional for a more translucent appearance.</p><p>Allow roughly <b>150 g</b> for these parts plus trials. Printed layers usually make clear filament look frosted; the actual result depends on settings and thickness.</p><a href="https://shop.polymaker.com/products/petg" target="_blank" rel="noopener">PETG · choose Clear ↗</a></article><article class="card"><span class="tag">Visible opaque parts</span><div class="swatch white"></div><h3>White PETG</h3><p>Print the structural plate, five individual command caps, wide cap, dial and foot. Ordinary white is appropriate here; it is not a replacement for clear agent caps.</p><p>Allow roughly <b>100 g</b>. Purchasing molded keycaps gives smoother surfaces and more reliable stem fit.</p><a href="https://shop.polymaker.com/products/petg" target="_blank" rel="noopener">PETG · choose White ↗</a></article><article class="card"><span class="tag">Light isolation</span><div class="swatch black"></div><h3>Black PETG</h3><p>Print six baffles, the touch cap and joystick cradle. The baffles keep one agent’s light from spilling into the next.</p><p>Allow roughly <b>50 g</b>. Existing black PLA can work for the internal baffles. Use adhesive rubber feet; TPU is optional, not required.</p><a href="https://shop.polymaker.com/products/petg" target="_blank" rel="noopener">PETG · choose Black ↗</a></article></div>
<p>These are material allowances, not slicer weight estimates. Three new spools may cost about <b>$55–85</b>, while this build uses only a fraction of each. Confirm <b>1.75 mm versus 2.85 mm</b> for your printer before ordering; the links default to 1.75 mm.</p><div class="note"><b>For faithful colors:</b> choose colorless filament. Tinted blue, gray, smoke, glitter and fiber-filled plastics change or block the light. Sand a test patch lightly for diffusion. Neither FDM PETG nor a printed keycap will exactly reproduce CNC-sandblasted polycarbonate or molded PBT. For the donor route, retain the factory lightpipe and use six frosted <a href="https://worklouder.cc/wrk-mx-pure">MX Pure caps</a>; the vendor listed those as a pre-order.</div>
<h3 style="margin-top:30px">Starting print profile</h3><div class="table-wrap"><table><thead><tr><th>Setting</th><th>Starting point</th><th>Reason / constraint</th></tr></thead><tbody><tr><td>Nozzle / layer height</td><td>0.4 mm / 0.20 mm</td><td>Use 0.10–0.12 mm for keycaps and 0.12–0.16 mm for the dial; 0.2 mm nozzle improves sockets if available.</td></tr><tr><td>Walls / top & bottom</td><td>4 perimeters / 5 layers</td><td>Use local solid modifiers around insert bosses and switch lands.</td></tr><tr><td>Infill</td><td>20–30% for opaque parts</td><td>Perimeter windows are modeled thin. Do not use sparse infill inside an optical window.</td></tr><tr><td>Temperature</td><td>Filament’s own PETG preset</td><td>Polymaker lists 240–260°C nozzle and 60–70°C bed; start within your printer’s supported range.</td></tr><tr><td>Moisture / plate</td><td>Dry filament; suitable release layer</td><td>Follow spool instructions. PETG can bond too strongly to smooth PEI or glass.</td></tr><tr><td>Bed size</td><td>At least 120 × 120 mm for one case</td><td>Largest part is 110 × 110 mm; allow for brim and actual printable area.</td></tr><tr><td>Scale</td><td>100%, millimetres</td><td>Adjust socket/cutout parameters instead of scaling the entire model.</td></tr></tbody></table></div><p class="caption">Filament guidance: <a href="https://shop.polymaker.com/products/petg">Polymaker PETG specifications</a>. Actual printer model, nozzle and calibrated tolerances remain unconfirmed.</p></section>
<section id="cad"><div class="eyebrow">03 / files you can use</div><h2>Editable solids. Printable meshes.</h2><div class="grid2"><div><p><b>11 unique printable files</b>, plus an assembled STEP model, parametric source and 3D preview. STL files are already rotated to their intended print orientation; STEP solids retain assembly coordinates.</p><p>The prototype uses <b>19.05 mm MX spacing</b>, a <b>94 mm faceplate</b>, <b>3 mm structural thickness</b> with <b>1.6 mm switch clip lands</b>, a <b>25 mm case</b> and a <b>5 mm removable circular foot</b>. Controls bring maximum overall height to about <b>46 mm</b>, plus rubber.</p><p><b>Accuracy boundary:</b> dimensions were selected from standard parts and the reference photo, not measured from the original. The CAD is not a manufacturer drawing. In particular, the joystick pocket, keycap sockets and printed insert holes require test fitting.</p><div class="downloads">__ASSEMBLY__ __PARAMS__ __SOURCE__ __GLB__</div><p class="caption">In the assembly, names beginning REF are purchased-part clearance envelopes. They are not objects to print. The STEP model does not contain a full production PCB or wires.</p></div><img class="preview" src="data:image/png;base64,__PREVIEW__" alt="CAD rendering of the custom keypad case with dial, six agent keys, command keys, wide key and joystick"></div>
<div class="table-wrap"><table><thead><tr><th>Part / print note</th><th>Qty</th><th>Material</th><th>Download</th></tr></thead><tbody>__CADROWS__</tbody></table></div>
<div class="note" style="margin-top:25px"><b>Print the two fit coupons first.</b> Trial a single switch, stem, and heat-set insert. The 3.9 mm insert pilot is for the specified 4.2 mm OD × 4 mm long Adafruit insert; it is a starting allowance, not a universal insert hole size. The full shell should follow a successful test.</div>
<h3 style="margin-top:28px">Add the key legends</h3><p>The CAD keycaps are blank. __LEGENDS__ provides six functional symbols at print scale; the artwork approximates the reference labels. Print at 100%, verify the 20 mm scale bar, and trim close to each icon. Apply to the five white 1U caps and the white wide mic cap. Leave the six translucent agent caps unmarked.</p><p>Optional <a href="https://www.hayespaper.com/products/inkjet-printer-waterslide-decal-paper">clear waterslide decal paper</a> works with an inkjet printer. Use the paper manufacturer’s sealing instructions, test the finish on a spare PETG cap, and keep coatings away from switch stems. A local print shop can make the decals if you do not have a paper printer. These are surface labels, not molded legends.</p><h3 style="margin-top:28px">To adapt the CAD for a genuine donor board</h3><p>Use __MEASURE__ to record the real board outline, hole pattern, component heights, port/button positions, optical parts and antenna clearance. Import the STEP into Fusion, FreeCAD, Onshape or another CAD tool; remove the hand-wiring supports, add measured PCB standoffs, and revise the port, battery and diffuser seats. A donor mounting revision is still required. Keeping the factory enclosure while using custom keycaps is the quickest way to preserve native functionality during this phase.</p><p>The supplied wide key has <b>two MX sockets 19.05 mm apart</b>. It fits two independent switches. A conventional single-center 2U keycap and stabilizer will not fit this plate. Two lighter switch springs may be preferable because the wide key presses both switches.</p></section>
<section id="parts"><div class="eyebrow">04 / shopping list</div><h2>Buy for one electronics route.</h2><p>Filter by route before buying. <b>Native</b> means genuine electronics for supported Codex features. <b>Custom</b> means the experimental hand-wired design and supplied CAD. <b>Materials</b> means filament. US-dollar figures are observed prices where shown, or labeled estimates; tax, shipping and tools are extra.</p><div class="filters" role="group" aria-label="Filter shopping list"><button data-filter="all" class="active">All items</button><button data-filter="native">Native route</button><button data-filter="custom">Custom route</button><button data-filter="materials">Filament</button></div><div class="progress" id="shopping-progress">0 items checked</div><div class="table-wrap"><table id="shopping"><thead><tr><th>✓</th><th>Part / seller link / specification</th><th>Buy / use</th><th>USD</th><th>Route</th></tr></thead><tbody>__BOM__</tbody></table></div><p class="caption">Check marks are saved in this browser when local storage is available. Supplier pages and stock can change. Catalog/search links for generic hardware require selecting the dimensions stated here.</p>
<div class="grid2" style="margin-top:25px"><div class="card"><h3>Custom build budget</h3><p class="callout-number">≈ $75–115</p><p>Electronics, small hardware and consumed materials, before shipping, tools and optional decal supplies. Add roughly $55–85 if buying three entire filament spools. The result still requires custom integration work for native parity.</p></div><div class="card"><h3>Tools & bench supplies</h3><p>Soldering iron with fine tip, flux, solder, ventilation, wire cutters/strippers, tweezers, multimeter, digital calipers, M3 hex driver, heat-set insertion tip, polyimide tape, thin removable foam tape and a small perfboard.</p><p>A filament dryer and a keycap puller help. No motors, display, speaker, Raspberry Pi computer, or onboard microphone are required.</p></div></div></section>
<section id="animation"><div class="eyebrow">Assembly / interactive 3D</div><h2>Watch the pieces come together.</h2><p>Play all eleven stages, use the timeline to separate the layers, and switch to the underside to inspect the hidden parts. Printed components use the same STEP geometry linked above.</p>__ANIMATION_FRAME__<div class="downloads">__ANIMATION_DOWNLOAD__</div><p class="caption">The animation shows the custom prototype. Purchased components and cable routes are simplified references; use the written instructions and wiring map for the build.</p></section><section id="assembly"><div class="eyebrow">05 / assembly</div><h2>Test the electronics before closing the case.</h2><h3>Native route: preserve the working assembly</h3><ol><li>Connect a genuine unit in its original case and complete the official setup. Confirm task colors and controls before changing hardware.</li><li>Measure with the donor worksheet. If opening a Pro unit, unplug USB, turn it off and disconnect the battery before moving the board. Keep its original charger, protection circuit and cell together.</li><li>Revise and test-print the mounting interface. Retain the factory switch/LED assembly and lightpipe. Provide access to USB and the rear button, clearance around the antenna, and a measured gap at the touch electrode.</li><li>Fit the revised shell without loading the PCB or pinching wires. Reconnect the original components and run the acceptance checklist below. The supplied custom-PCB-free case is not approved for this transplant.</li></ol>
<h3 style="margin-top:35px">Custom route: supplied Rev A geometry</h3><div class="steps">
<article class="step"><h3>Print the fit samples</h3><p>Print files 10 and 11 in the chosen materials. Check the 14.0 / 14.1 / 14.2 mm switch apertures. The switch should click in securely without forcing. Test the MX cross and heat-set insert. Change the JSON parameters and regenerate if necessary.</p></article>
<article class="step"><h3>Print and finish the body</h3><p>Print the case open side up, plate face down, foot bottom down, and baffles open side up. Clean burrs without widening switch lands. Keep the eight thin optical windows intact. Trial the USB cable in the 15 × 8 mm tunnel.</p></article>
<article class="step"><h3>Install the inserts</h3><p>Heat-set four inserts from the tops of the corner posts and two into the underside foot mounts. Use the 4 mm-long specified insert and let each cool fully. Keep the iron away from the thin windows.</p></article>
<article class="step"><h3>Fit switches and controls</h3><p>Clip 13 normal MX switches into the plate. Fasten the encoder with its washer and M7 nut; do not overtighten plastic. Test the dial with the supplied knob first. Solder flexible leads onto the slide joystick, test its movement, and seat it in the printed tray. Trim only tray plastic if required; do not remove the joystick’s retention frame.</p></article>
<article class="step"><h3>Wire the key matrix</h3><p>Use the top-view matrix below. One switch terminal joins its column. The other goes to the unbanded end of its diode; the banded end joins the row. Insulate crossings. Wire both switches under the wide key independently—the firmware merges them.</p></article>
<article class="step"><h3>Build the light chain</h3><p>Use two packs of the specified RGBW pixels. Put LEDs 0–5 into six black baffles, shining upward; insulate their rear pads. Tack baffles to the plate underside after wiring. Face LEDs 6–13 outward through the case’s eight inner-wall pockets. Chain DOUT to DIN and use common power/ground buses.</p></article>
<article class="step"><h3>Add touch and indicators</h3><p>Cut a 13 mm copper disk and solder its lead before installing it beneath the touch cap’s thin top skin. Run it to D10 with a 1 MΩ resistor to ground. Secure the cap by its flange. Fit the three 3 mm indicator LEDs with one 1 kΩ resistor each.</p></article>
<article class="step"><h3>Mount the controller</h3><p>KB2040 lies between the guide rails, USB facing rear. Use approximately 1.6 mm insulating foam tape under it; its nominal envelope is 17.8 × 35 × 4.9 mm. Solder wires directly to pads, not tall headers. Secure a maximum 25 × 20 mm perfboard in the front internal bay for the level shifter and passives.</p></article>
<article class="step"><h3>Power and program on the bench</h3><p>Check for shorts and diode polarity with a multimeter. Connect USB with the plate still accessible. Install CircuitPython and the included files. Test every switch, both wide-key halves, joystick axes, encoder/button, touch and every RGBW pixel. LEDs remain brightness-limited to 15%.</p></article>
<article class="step"><h3>Close and fit the foot</h3><p>Allow service slack without trapping wires under baffles, switches or posts. Fasten the plate with four M3 × 8 screws. Optionally tape four 24 mm OD, ≤2 mm-thick steel washers into the foot pockets. Attach the foot with two low-profile M3 × 8 screws and add adhesive rubber at the perimeter. Fit keycaps last.</p></article>
</div><div class="notice"><strong>Prototype fit checks that need the actual parts</strong>The slide joystick has no controlled supplier drawing; test its 19.8 mm pocket. Keycap sockets depend on printer calibration. At full key travel, caps must clear the plate and each other. The dial must rotate freely and still depress. LED solder joints must not touch switch pins. No physical print or electrical bench test has been performed here.</div>
<h3>Matrix: view from above, USB at the rear</h3><div class="table-wrap"><table><thead><tr><th>Row / GPIO</th><th>C1 / D6</th><th>C2 / D7</th><th>C3 / D8</th><th>C4 / D9</th></tr></thead><tbody><tr><td>R1 / D2</td><td>Encoder, separate wiring</td><td>Agent 01</td><td>Agent 02</td><td>Joystick, separate wiring</td></tr><tr><td>R2 / D3</td><td>Agent 03</td><td>Agent 04</td><td>Agent 05</td><td>Agent 06</td></tr><tr><td>R3 / D4</td><td>Command 1</td><td>Command 2</td><td>Command 3</td><td>Command 4</td></tr><tr><td>R4 / D5</td><td>Touch, separate wiring</td><td>Wide key / left switch</td><td>Wide key / right switch</td><td>Command 6</td></tr></tbody></table></div><p class="caption">When soldering from underneath, this layout is mirrored left-to-right. Label rows and columns before flipping the plate.</p>
<h3 style="margin-top:30px">Electrical connection map</h3><div class="diagram">__WIRING__</div><div class="downloads">__WIRINGDL__ __BOMDL__</div>
<div class="grid2"><div class="card"><h3>Keep power domains correct</h3><p>Power pixels and the 74AHCT125 from the KB2040’s fused RAW rail. Power the joystick from 3V so its analog outputs stay within 3.3 V. All grounds join. Leave the fuse-bypass jumper open.</p><p>Budget estimate: 14 × 75 mA × 15% ≈ 158 mA for the LEDs at the worst RGBW setting, plus board and indicators. Target under 250 mA total and verify with a USB meter. This is an estimate, not a measured result.</p><p>Put a 100 µF / ≥10 V capacitor across the LED rail and 100 nF close to the shifter’s supply pins. Do not add an external supply to this USB-powered build.</p></div><div class="card"><h3>Joystick and encoder pinout</h3><p>On SparkFun’s COM-09426, the bottom-view pad sequence is X, VCC, Y, GND; GND is nearest the two mounting tabs. Use the linked seller’s orientation diagram and a meter—other PSP replacements may differ. Despite the seller’s Arduino example, this build uses <b>3.3 V</b> VCC.</p><p>Encoder A/B go to TX/RX and common to GND. Its separate switch goes between A2 and GND. If turn direction is reversed, swap A/B in firmware. No resistor is needed for the encoder switch because the firmware enables its pull-up.</p></div></div><p class="caption">Electrical sources: <a href="https://learn.adafruit.com/adafruit-kb2040/pinouts">KB2040 pinout</a> · <a href="https://learn.adafruit.com/neopixel-levelshifter/shifting-levels">LED level shifting</a> · <a href="https://www.sparkfun.com/thumb-slide-joystick.html">Joystick</a> · <a href="https://cdn-shop.adafruit.com/datasheets/pec11.pdf">Encoder drawing</a>.</p></section>
<section id="software"><div class="eyebrow">06 / software and light behavior</div><h2>Colors must follow real task state.</h2><div class="grid2"><div><h3>Native setup</h3><p>Use the current desktop app, connect the genuine unit, and follow its detected-device setup. On macOS, grant the requested Input Monitoring access. Choose task assignments, controls and brightness in the device settings. Work Louder Input is optional for other-app layers.</p><p>The mic key uses the computer’s microphone. Native voice feedback uses a sea-green recording animation, followed by white processing and ready feedback.</p><p><a href="https://learn.chatgpt.com/docs/features/codex-micro" target="_blank" rel="noopener">Complete official setup and behavior reference ↗</a></p></div><div class="card"><h3>State → agent-key color</h3><div class="status-line"><i class="dot" style="--c:#f9faf5"></i><b>White</b> · idle</div><div class="status-line"><i class="dot" style="--c:#4a92ff"></i><b>Blue</b> · working</div><div class="status-line"><i class="dot" style="--c:#63ce82"></i><b>Green</b> · completed, unread</div><div class="status-line"><i class="dot" style="--c:#ffbd58"></i><b>Amber</b> · input required</div><div class="status-line"><i class="dot" style="--c:#f3656a"></i><b>Red</b> · error</div><div class="status-line"><i class="dot" style="--c:#829284"></i><b>Off</b> · unassigned</div><p class="caption">The selected task pulses. The current guide specifies red for errors; the supply-page photography can look pink. RGB values in the illustration are approximations, not published firmware constants.</p></div></div>
<h3 style="margin-top:30px">Install the custom prototype firmware</h3><p>Only do this on the <b>KB2040</b>. These files are not compatible with the genuine Work Louder board and must not replace its firmware.</p><ol><li>Install the stable <a href="https://circuitpython.org/board/adafruit_kb2040/">CircuitPython build for Adafruit KB2040</a> using its BOOT + USB bootloader procedure.</li><li>From the matching <a href="https://circuitpython.org/libraries">CircuitPython library bundle</a>, copy <code>adafruit_hid/</code>, <code>neopixel.mpy</code>, and <code>adafruit_pixelbuf.mpy</code> into <code>CIRCUITPY/lib/</code>.</li><li>Copy <code>boot.py</code>, <code>code.py</code>, and <code>logic.py</code> to CIRCUITPY. Unplug/replug so the second USB serial port is enabled. Keep hands off the stick and touch pad during startup calibration.</li><li>Agent and command keys output F13–F24. The touch control chooses plain, Shift, or Control banks. Map these in your shortcut utility or edit the mappings. The dial scrolls and presses Enter; the joystick sends arrows.</li><li>Install Python’s <code>pyserial</code> on the computer and use the included helper to set individual light colors.</li></ol>
<div class="downloads">__BOOT__ __CODE__ __LOGIC__ __LIGHT__</div><pre><code>python -m pip install pyserial
python -m serial.tools.list_ports
# Pick the KB2040 DATA port, not its REPL/console port.
python tools/set_light.py /dev/cu.usbmodemXXXX 0 0 120 255
# Windows example: replace the device path with COM7.
# LED 0–5 = agent keys; LED 6–13 = perimeter.
</code></pre>
<p class="caption">The helper sends a manual color command. Seeing the right color confirms LED control, not live task synchronization. Default bank colors are not agent-status indicators.</p>
<h3 style="margin-top:30px">Work remaining for custom full functionality</h3><p>A host integration must obtain live task identities and lifecycle events, map six keys consistently, send status and selection updates, handle voice states, dispatch app actions, and recover after reconnects. Native settings, reasoning controls, approval actions and Bluetooth add separate work. The installed app’s Work Louder library confirms a vendor RPC connection for device events and thread lighting; the supplied generic HID firmware does not implement that connection.</p><p><b>No tested custom bridge or native-device emulation is included.</b> A periodic notification script is insufficient to match the original. Completion requires tests on the actual hardware and the current desktop app. The genuine electronics route avoids this unimplemented software layer.</p></section>
<section id="checks"><div class="eyebrow">07 / verification and remaining decisions</div><h2>What has been checked.</h2><div class="grid2"><div class="card"><h3>Completed offline</h3><p>All 11 STL files are closed, single-volume meshes. Individual STEP solids pass the CAD kernel validity check. The tested assembly pairs have no material overlap. The board envelope clears the case.</p><p>Input-state tests cover the wide key’s two-switch press/release ordering, joystick dead-zone behavior and malformed color input. Firmware syntax is checked.</p><div class="downloads">__VALIDATION__</div><small>These tests do not establish print fit, soldering correctness, optical uniformity, key travel feel, electrical current, firmware operation on hardware, or OEM donor compatibility.</small></div><div class="card"><h3>Still needed from the build</h3><p>Printer model, material diameter and nozzle; choice of genuine or custom electronics; actual-part measurements; first fit coupons; assembled hardware; and end-to-end software tests.</p><p>Native functionality is documented for genuine devices, but this particular printed re-housing has not been built. The custom route’s native software parity remains unimplemented.</p></div></div>
<h3 style="margin-top:30px">Bench acceptance checklist</h3><div class="grid2 checklist"><div><label><input type="checkbox">All switches clip in; caps clear at full travel.</label><label><input type="checkbox">Wide key produces one press and release.</label><label><input type="checkbox">Dial rotates, presses and springs back.</label><label><input type="checkbox">Joystick reaches all directions without binding.</label><label><input type="checkbox">Touch works through the finished cap.</label><label><input type="checkbox">All 14 custom pixels respond in the correct order.</label><label><input type="checkbox">One key’s light does not obscure adjacent status.</label><label><input type="checkbox">USB current and component temperatures are normal.</label></div><div><label><input type="checkbox">Native device is detected after a cold reconnect.</label><label><input type="checkbox">Six task assignments stay aligned with their keys.</label><label><input type="checkbox">Idle, work, completion, input and error colors match.</label><label><input type="checkbox">Selected-key pulse and dimming behave correctly.</label><label><input type="checkbox">Approve, decline, new-chat and send actions work.</label><label><input type="checkbox">Voice press/hold and perimeter feedback work.</label><label><input type="checkbox">Reasoning dial and joystick app actions work.</label><label><input type="checkbox">Pro Bluetooth reconnect and charging still work.</label></div></div><p class="caption">The native column is a future physical acceptance test, not a statement that the custom firmware passes it.</p></section>
<footer class="footer">Independent DIY reconstruction based on the linked OpenAI and Work Louder product references. Not affiliated with either manufacturer. Checked 06 September 2026. The HTML embeds its CAD/source downloads, preview and assembly player; it can be kept as one file. The embedded ZIP contains the CAD and supporting files; the full delivery ZIP also includes this guide.</footer>
</main><script>
const palette={idle:['#f9faf5','Idle'],thinking:['#4a92ff','Thinking'],complete:['#63ce82','Complete'],input:['#ffbd58','Needs input'],error:['#f3656a','Error'],off:['#899e90','Off']};
const states=['thinking','idle','complete','input','error','off'];let selected=0;
function paint(){document.querySelectorAll('[data-agent]').forEach((b,i)=>{b.style.setProperty('--glow',palette[states[i]][0]);b.classList.toggle('selected',i===selected);b.setAttribute('aria-pressed',String(i===selected));});document.querySelector('.sim-status').textContent='Agent '+String(selected+1).padStart(2,'0')+' · '+palette[states[selected]][1];}
document.querySelectorAll('[data-agent]').forEach(b=>b.addEventListener('click',()=>{selected=Number(b.dataset.agent);paint()}));document.querySelectorAll('[data-state]').forEach(b=>b.addEventListener('click',()=>{states[selected]=b.dataset.state;paint()}));paint();
document.querySelectorAll('[data-filter]').forEach(b=>b.addEventListener('click',()=>{document.querySelectorAll('[data-filter]').forEach(x=>x.classList.toggle('active',x===b));document.querySelectorAll('#shopping tbody tr').forEach(r=>r.classList.toggle('hidden',b.dataset.filter!=='all'&&r.dataset.route!==b.dataset.filter));}));
const boxes=[...document.querySelectorAll('input[type=checkbox]')];let saved={};try{saved=JSON.parse(localStorage.getItem('diy-micro-checklist-v1')||'{}')}catch(e){};function updateCount(){const n=document.querySelectorAll('#shopping input:checked').length;document.getElementById('shopping-progress').textContent=n+' shopping items checked';}boxes.forEach((b,i)=>{b.checked=!!saved[i];b.addEventListener('change',()=>{saved[i]=b.checked;try{localStorage.setItem('diy-micro-checklist-v1',JSON.stringify(saved))}catch(e){}updateCount()})});updateCount();
</script></body></html>'''
animation_frame='<iframe class="assembly-frame" title="Interactive 3D assembly animation" loading="lazy" srcdoc="'+html.escape((ROOT/'assembly-animation.html').read_text(),quote=True)+'"></iframe>'
replacements={'__ANIMATION_FRAME__':animation_frame,'__ANIMATION_DOWNLOAD__':dl('assembly-animation.html','Download standalone assembly animation'),'__LEGENDS__':dl('docs/key-legends.svg','Key legend SVG'),'__ZIP__':zip_data,'__CADROWS__':rows,'__BOM__':bom,'__PREVIEW__':preview,'__WIRING__':wiring,'__ASSEMBLY__':dl('step/assembly.step','Assembly STEP'),'__PARAMS__':dl('cad/parameters.json','Parameters JSON'),'__SOURCE__':dl('cad/build.py','CAD Python source'),'__GLB__':dl('cad/preview.glb','3D preview GLB'),'__MEASURE__':dl('docs/oem-measurements.csv','the donor measurement worksheet'),'__WIRINGDL__':dl('docs/wiring.svg','Wiring diagram SVG'),'__BOMDL__':dl('docs/bom.csv','Shopping list CSV'),'__BOOT__':dl('firmware/boot.py'),'__CODE__':dl('firmware/code.py'),'__LOGIC__':dl('firmware/logic.py'),'__LIGHT__':dl('tools/set_light.py'),'__VALIDATION__':dl('docs/validation.json','Validation report')}
for a,b in replacements.items():page=page.replace(a,b)
(ROOT/'build-guide.html').write_text(page)
print('Wrote self-contained HTML:',round(len(page)/1024/1024,1),'MB')
